Shaperon-g/AutoWatering-ch32v003/src/core/ch32v00x.h

/********************************** (C) COPYRIGHT  *******************************
 * File Name          : ch32v00x.h
 * Author             : Shaperon
 * Version            : V1.0
 * Date               : 13/06/2026
 * Description        : CH32V00x Modified file
 *********************************************************************************
 * The original file was most likely copied from another chip somewhere 
 * does not match the datasheet, so I redid it.
 * P.S. I also cleaned up a bit of the junk, so this
 * **NOT INTERCHANGEABLE with the official SDK and SPL**
 * 
 * Оригинальный файл скорее всего скопипащен с другого чипа и где-то 
 * несоответствует даташиту, поэтому я его переделал.
 * p.s. Я в целом еще немного мусора почистил, так что это 
 * **НЕ ВЗАИМОЗАМЕНЯЕМО с оф. SDK и SPL** 
 *******************************************************************************/
#ifndef __CH32V00x_H
#define __CH32V00x_H

#ifdef __cplusplus
extern "C" {
#endif

/* Interrupt Number Definition, according to the selected device */
typedef enum IRQn
{
    /******  RISC-V Processor Exceptions Numbers *******************************************************/
    NonMaskableInt_IRQn = 2, /* 2 Non Maskable Interrupt                             */
    EXC_IRQn = 3,            /* 3 Exception Interrupt                                */
    SysTick_IRQn = 12,       /* 12 System timer Interrupt                            */
    Software_IRQn = 14,      /* 14 software Interrupt                                */

    /******  RISC-V specific Interrupt Numbers *********************************************************/
    WWDG_IRQn = 16,          /* Window WatchDog Interrupt                            */
    PVD_IRQn = 17,           /* PVD through EXTI Line detection Interrupt            */
    FLASH_IRQn = 18,         /* FLASH global Interrupt                               */
    RCC_IRQn = 19,           /* RCC global Interrupt                                 */
    EXTI7_0_IRQn = 20,       /* External Line[7:0] Interrupts                        */
    AWU_IRQn = 21,           /* AWU global Interrupt                                 */
    DMA1_Channel1_IRQn = 22, /* DMA1 Channel 1 global Interrupt                      */
    DMA1_Channel2_IRQn = 23, /* DMA1 Channel 2 global Interrupt                      */
    DMA1_Channel3_IRQn = 24, /* DMA1 Channel 3 global Interrupt                      */
    DMA1_Channel4_IRQn = 25, /* DMA1 Channel 4 global Interrupt                      */
    DMA1_Channel5_IRQn = 26, /* DMA1 Channel 5 global Interrupt                      */
    DMA1_Channel6_IRQn = 27, /* DMA1 Channel 6 global Interrupt                      */
    DMA1_Channel7_IRQn = 28, /* DMA1 Channel 7 global Interrupt                      */
    ADC_IRQn = 29,           /* ADC global Interrupt                                 */
    I2C1_EV_IRQn = 30,       /* I2C1 Event Interrupt                                 */
    I2C1_ER_IRQn = 31,       /* I2C1 Error Interrupt                                 */
    USART1_IRQn = 32,        /* USART1 global Interrupt                              */
    SPI1_IRQn = 33,          /* SPI1 global Interrupt                                */
    TIM1_BRK_IRQn = 34,      /* TIM1 Break Interrupt                                 */
    TIM1_UP_IRQn = 35,       /* TIM1 Update Interrupt                                */
    TIM1_TRG_COM_IRQn = 36,  /* TIM1 Trigger and Commutation Interrupt               */
    TIM1_CC_IRQn = 37,       /* TIM1 Capture Compare Interrupt                       */
    TIM2_IRQn = 38,          /* TIM2 global Interrupt                                */

} IRQn_Type;

#define HardFault_IRQn    EXC_IRQn

#include <stdint.h>
#include <core_riscv.h>
//#include <system_ch32v00x.h>

/* Analog to Digital Converter */
typedef struct
{
    __IO uint32_t STATR;
    __IO uint32_t CTLR1;
    __IO uint32_t CTLR2;
    __IO uint32_t SAMPTR1;
    __IO uint32_t SAMPTR2;
    __IO uint32_t IOFR1;
    __IO uint32_t IOFR2;
    __IO uint32_t IOFR3;
    __IO uint32_t IOFR4;
    __IO uint32_t WDHTR;
    __IO uint32_t WDLTR;
    __IO uint32_t RSQR1;
    __IO uint32_t RSQR2;
    __IO uint32_t RSQR3;
    __IO uint32_t ISQR;
    __IO uint32_t IDATAR1;
    __IO uint32_t IDATAR2;
    __IO uint32_t IDATAR3;
    __IO uint32_t IDATAR4;
    __IO uint32_t RDATAR;
    __IO uint32_t DLYR;
} ADC_TypeDef;

/* Debug MCU */
typedef struct
{
    __IO uint32_t CFGR0;
    __IO uint32_t CFGR1;
} DBGMCU_TypeDef;

/* DMA Controller */
typedef struct
{
    __IO uint32_t CFGR;
    __IO uint32_t CNTR;
    __IO uint32_t PADDR;
    __IO uint32_t MADDR;
} DMA_Channel_TypeDef;

typedef struct
{
    __IO uint32_t INTFR;
    __IO uint32_t INTFCR;
} DMA_TypeDef;

/* External Interrupt/Event Controller */
typedef struct
{
    __IO uint32_t INTENR;
    __IO uint32_t EVENR;
    __IO uint32_t RTENR;
    __IO uint32_t FTENR;
    __IO uint32_t SWIEVR;
    __IO uint32_t INTFR;
} EXTI_TypeDef;

/* FLASH Registers */
typedef struct
{
    __IO uint32_t ACTLR;
    __IO uint32_t KEYR;
    __IO uint32_t OBKEYR;
    __IO uint32_t STATR;
    __IO uint32_t CTLR;
    __IO uint32_t ADDR;
    __IO uint32_t RESERVED;
    __IO uint32_t OBR;
    __IO uint32_t WPR;
    __IO uint32_t MODEKEYR;
    __IO uint32_t BOOT_MODEKEYR;
} FLASH_TypeDef;

/* Option Bytes Registers */
typedef struct
{
    __IO uint16_t RDPR;
    __IO uint16_t USER;
    __IO uint16_t DATA0;
    __IO uint16_t DATA1;
    __IO uint16_t WRPR0;
    __IO uint16_t WRPR1;
} OB_TypeDef;

/* General Purpose I/O */
typedef struct
{
    __IO uint32_t CFGLR;
    __IO uint32_t CFGHR;
    __IO uint32_t INDR;
    __IO uint32_t OUTDR;
    __IO uint32_t BSHR;
    __IO uint32_t BCR;
    __IO uint32_t LCKR;
} GPIO_TypeDef;

/* Alternate Function I/O */
typedef struct
{
    uint32_t RESERVED0;
    __IO uint32_t PCFR1;
    __IO uint32_t EXTICR;
} AFIO_TypeDef;

/* Inter Integrated Circuit Interface */
typedef struct
{
    __IO uint16_t CTLR1;
    uint16_t      RESERVED0;
    __IO uint16_t CTLR2;
    uint16_t      RESERVED1;
    __IO uint16_t OADDR1;
    uint16_t      RESERVED2;
    __IO uint16_t OADDR2;
    uint16_t      RESERVED3;
    __IO uint16_t DATAR;
    uint16_t      RESERVED4;
    __IO uint16_t STAR1;
    uint16_t      RESERVED5;
    __IO uint16_t STAR2;
    uint16_t      RESERVED6;
    __IO uint16_t CKCFGR;
    uint16_t      RESERVED7;
} I2C_TypeDef;

/* Independent WatchDog */
typedef struct
{
    __IO uint32_t CTLR;
    __IO uint32_t PSCR;
    __IO uint32_t RLDR;
    __IO uint32_t STATR;
} IWDG_TypeDef;

/* Power Control */
typedef struct
{
    __IO uint32_t CTLR;
    __IO uint32_t CSR;
    __IO uint32_t AWUCSR;
    __IO uint32_t AWUWR;
    __IO uint32_t AWUPSC;
} PWR_TypeDef;

/* Reset and Clock Control */
typedef struct
{
    __IO uint32_t CTLR;
    __IO uint32_t CFGR0;
    __IO uint32_t INTR;
    __IO uint32_t APB2PRSTR;
    __IO uint32_t APB1PRSTR;
    __IO uint32_t AHBPCENR;
    __IO uint32_t APB2PCENR;
    __IO uint32_t APB1PCENR;
    __IO uint32_t RESERVED0;
    __IO uint32_t RSTSCKR;
} RCC_TypeDef;

/* Serial Peripheral Interface */
typedef struct
{
    __IO uint16_t CTLR1;
    uint16_t      RESERVED0;
    __IO uint16_t CTLR2;
    uint16_t      RESERVED1;
    __IO uint16_t STATR;
    uint16_t      RESERVED2;
    __IO uint16_t DATAR;
    uint16_t      RESERVED3;
    __IO uint16_t CRCR;
    uint16_t      RESERVED4;
    __IO uint16_t RCRCR;
    uint16_t      RESERVED5;
    __IO uint16_t TCRCR;
    uint16_t      RESERVED6;
    uint32_t      RESERVED7;
    uint32_t      RESERVED8;
    __IO uint16_t HSCR;
    uint16_t      RESERVED9;
} SPI_TypeDef;

/* TIM */
typedef struct
{
    __IO uint16_t CTLR1;
    uint16_t      RESERVED0;
    __IO uint16_t CTLR2;
    uint16_t      RESERVED1;
    __IO uint16_t SMCFGR;
    uint16_t      RESERVED2;
    __IO uint16_t DMAINTENR;
    uint16_t      RESERVED3;
    __IO uint16_t INTFR;
    uint16_t      RESERVED4;
    __IO uint16_t SWEVGR;
    uint16_t      RESERVED5;
    __IO uint16_t CHCTLR1;
    uint16_t      RESERVED6;
    __IO uint16_t CHCTLR2;
    uint16_t      RESERVED7;
    __IO uint16_t CCER;
    uint16_t      RESERVED8;
    __IO uint16_t CNT;
    uint16_t      RESERVED9;
    __IO uint16_t PSC;
    uint16_t      RESERVED10;
    __IO uint16_t ATRLR;
    uint16_t      RESERVED11;
    __IO uint16_t RPTCR;
    uint16_t      RESERVED12;
    __IO uint32_t CH1CVR;
    __IO uint32_t CH2CVR;
    __IO uint32_t CH3CVR;
    __IO uint32_t CH4CVR;
    __IO uint16_t BDTR;
    uint16_t      RESERVED13;
    __IO uint16_t DMACFGR;
    uint16_t      RESERVED14;
    __IO uint16_t DMAADR;
    uint16_t      RESERVED15;
} TIM_TypeDef;

/* Universal Synchronous Asynchronous Receiver Transmitter */
typedef struct
{
    __IO uint16_t STATR;
    uint16_t      RESERVED0;
    __IO uint16_t DATAR;
    uint16_t      RESERVED1;
    __IO uint16_t BRR;
    uint16_t      RESERVED2;
    __IO uint16_t CTLR1;
    uint16_t      RESERVED3;
    __IO uint16_t CTLR2;
    uint16_t      RESERVED4;
    __IO uint16_t CTLR3;
    uint16_t      RESERVED5;
    __IO uint16_t GPR;
    uint16_t      RESERVED6;
} USART_TypeDef;

/* Window WatchDog */
typedef struct
{
    __IO uint32_t CTLR;
    __IO uint32_t CFGR;
    __IO uint32_t STATR;
} WWDG_TypeDef;

/* Enhanced Registers */
typedef struct
{
    __IO uint32_t EXTEN_CTR;
} EXTEN_TypeDef;

/* Peripheral memory map */
#define FLASH_BASE                              ((uint32_t)0x08000000) /* FLASH base address in the alias region */
#define SRAM_BASE                               ((uint32_t)0x20000000) /* SRAM base address in the alias region */
#define PERIPH_BASE                             ((uint32_t)0x40000000) /* Peripheral base address in the alias region */

#define APB1PERIPH_BASE                         (PERIPH_BASE)
#define APB2PERIPH_BASE                         (PERIPH_BASE + 0x10000)
#define AHBPERIPH_BASE                          (PERIPH_BASE + 0x20000)

#define TIM2_BASE                               (APB1PERIPH_BASE + 0x0000)
#define WWDG_BASE                               (APB1PERIPH_BASE + 0x2C00)
#define IWDG_BASE                               (APB1PERIPH_BASE + 0x3000)
#define I2C1_BASE                               (APB1PERIPH_BASE + 0x5400)
#define PWR_BASE                                (APB1PERIPH_BASE + 0x7000)

#define AFIO_BASE                               (APB2PERIPH_BASE + 0x0000)
#define EXTI_BASE                               (APB2PERIPH_BASE + 0x0400)
#define GPIOA_BASE                              (APB2PERIPH_BASE + 0x0800)
#define GPIOC_BASE                              (APB2PERIPH_BASE + 0x1000)
#define GPIOD_BASE                              (APB2PERIPH_BASE + 0x1400)
#define ADC1_BASE                               (APB2PERIPH_BASE + 0x2400)
#define TIM1_BASE                               (APB2PERIPH_BASE + 0x2C00)
#define SPI1_BASE                               (APB2PERIPH_BASE + 0x3000)
#define USART1_BASE                             (APB2PERIPH_BASE + 0x3800)

#define DMA1_BASE                               (AHBPERIPH_BASE + 0x0000)
#define DMA1_Channel1_BASE                      (AHBPERIPH_BASE + 0x0008)
#define DMA1_Channel2_BASE                      (AHBPERIPH_BASE + 0x001C)
#define DMA1_Channel3_BASE                      (AHBPERIPH_BASE + 0x0030)
#define DMA1_Channel4_BASE                      (AHBPERIPH_BASE + 0x0044)
#define DMA1_Channel5_BASE                      (AHBPERIPH_BASE + 0x0058)
#define DMA1_Channel6_BASE                      (AHBPERIPH_BASE + 0x006C)
#define DMA1_Channel7_BASE                      (AHBPERIPH_BASE + 0x0080)
#define RCC_BASE                                (AHBPERIPH_BASE + 0x1000)

#define FLASH_R_BASE                            (AHBPERIPH_BASE + 0x2000) /* Flash registers base address */
#define OB_BASE                                 ((uint32_t)0x1FFFF800)    /* Flash Option Bytes base address */
#define EXTEN_BASE                              ((uint32_t)0x40023800)

/* Peripheral declaration */
#define TIM2                                    ((TIM_TypeDef *)TIM2_BASE)
#define WWDG                                    ((WWDG_TypeDef *)WWDG_BASE)
#define IWDG                                    ((IWDG_TypeDef *)IWDG_BASE)
#define I2C1                                    ((I2C_TypeDef *)I2C1_BASE)
#define PWR                                     ((PWR_TypeDef *)PWR_BASE)
#define AFIO                                    ((AFIO_TypeDef *)AFIO_BASE)
#define EXTI                                    ((EXTI_TypeDef *)EXTI_BASE)
#define GPIOA                                   ((GPIO_TypeDef *)GPIOA_BASE)
#define GPIOC                                   ((GPIO_TypeDef *)GPIOC_BASE)
#define GPIOD                                   ((GPIO_TypeDef *)GPIOD_BASE)
#define ADC1                                    ((ADC_TypeDef *)ADC1_BASE)
#define TIM1                                    ((TIM_TypeDef *)TIM1_BASE)
#define SPI1                                    ((SPI_TypeDef *)SPI1_BASE)
#define USART1                                  ((USART_TypeDef *)USART1_BASE)
#define DMA1                                    ((DMA_TypeDef *)DMA1_BASE)
#define DMA1_Channel1                           ((DMA_Channel_TypeDef *)DMA1_Channel1_BASE)
#define DMA1_Channel2                           ((DMA_Channel_TypeDef *)DMA1_Channel2_BASE)
#define DMA1_Channel3                           ((DMA_Channel_TypeDef *)DMA1_Channel3_BASE)
#define DMA1_Channel4                           ((DMA_Channel_TypeDef *)DMA1_Channel4_BASE)
#define DMA1_Channel5                           ((DMA_Channel_TypeDef *)DMA1_Channel5_BASE)
#define DMA1_Channel6                           ((DMA_Channel_TypeDef *)DMA1_Channel6_BASE)
#define DMA1_Channel7                           ((DMA_Channel_TypeDef *)DMA1_Channel7_BASE)
#define RCC                                     ((RCC_TypeDef *)RCC_BASE)
#define FLASH                                   ((FLASH_TypeDef *)FLASH_R_BASE)
#define OB                                      ((OB_TypeDef *)OB_BASE)
#define EXTEN                                   ((EXTEN_TypeDef *)EXTEN_BASE)

/******************************************************************************/
/*                         Peripheral Registers Bits Definition               */
/******************************************************************************/

/******************************************************************************/
/*                        Analog to Digital Converter                         */
/******************************************************************************/

/********************  Bit definition for ADC_STATR register  ********************/
#define ADC_AWD                                 ((uint8_t)0x01) /* Analog watchdog flag */
#define ADC_EOC                                 ((uint8_t)0x02) /* End of conversion */
#define ADC_JEOC                                ((uint8_t)0x04) /* Injected channel end of conversion */
#define ADC_JSTRT                               ((uint8_t)0x08) /* Injected channel Start flag */
#define ADC_STRT                                ((uint8_t)0x10) /* Regular channel Start flag */

/*******************  Bit definition for ADC_CTLR1 register  ********************/
#define ADC_AWDCH                               ((uint32_t)0x0000001F) /* AWDCH[4:0] bits (Analog watchdog channel select bits) */
#define ADC_AWDCH_0                             ((uint32_t)0x00000001) /* Bit 0 */
#define ADC_AWDCH_1                             ((uint32_t)0x00000002) /* Bit 1 */
#define ADC_AWDCH_2                             ((uint32_t)0x00000004) /* Bit 2 */
#define ADC_AWDCH_3                             ((uint32_t)0x00000008) /* Bit 3 */
#define ADC_AWDCH_4                             ((uint32_t)0x00000010) /* Bit 4 */

#define ADC_EOCIE                               ((uint32_t)0x00000020) /* Interrupt enable for EOC */
#define ADC_AWDIE                               ((uint32_t)0x00000040) /* Analog Watchdog interrupt enable */
#define ADC_JEOCIE                              ((uint32_t)0x00000080) /* Interrupt enable for injected channels */
#define ADC_SCAN                                ((uint32_t)0x00000100) /* Scan mode */
#define ADC_AWDSGL                              ((uint32_t)0x00000200) /* Enable the watchdog on a single channel in scan mode */
#define ADC_JAUTO                               ((uint32_t)0x00000400) /* Automatic injected group conversion */
#define ADC_DISCEN                              ((uint32_t)0x00000800) /* Discontinuous mode on regular channels */
#define ADC_JDISCEN                             ((uint32_t)0x00001000) /* Discontinuous mode on injected channels */

#define ADC_DISCNUM                             ((uint32_t)0x0000E000) /* DISCNUM[2:0] bits (Discontinuous mode channel count) */
#define ADC_DISCNUM_0                           ((uint32_t)0x00002000) /* Bit 0 */
#define ADC_DISCNUM_1                           ((uint32_t)0x00004000) /* Bit 1 */
#define ADC_DISCNUM_2                           ((uint32_t)0x00008000) /* Bit 2 */

#define ADC_JAWDEN                              ((uint32_t)0x00400000) /* Analog watchdog enable on injected channels */
#define ADC_AWDEN                               ((uint32_t)0x00800000) /* Analog watchdog enable on regular channels */

#define ADC_CALVOL                              ((uint32_t)0x06000000) /* Calibration voltage selection */
#define ADC_CALVOL_0                            ((uint32_t)0x02000000) /* Bit 0 */
#define ADC_CALVOL_1                            ((uint32_t)0x04000000) /* Bit 1 */

/*******************  Bit definition for ADC_CTLR2 register  ********************/
#define ADC_ADON                                ((uint32_t)0x00000001) /* A/D Converter ON / OFF */
#define ADC_CONT                                ((uint32_t)0x00000002) /* Continuous Conversion */
#define ADC_CAL                                 ((uint32_t)0x00000004) /* A/D Calibration */
#define ADC_RSTCAL                              ((uint32_t)0x00000008) /* Reset Calibration */
#define ADC_DMA                                 ((uint32_t)0x00000100) /* Direct Memory access mode */
#define ADC_ALIGN                               ((uint32_t)0x00000800) /* Data Alignment */

#define ADC_JEXTSEL                             ((uint32_t)0x00007000) /* JEXTSEL[2:0] bits (External event select for injected group) */
#define ADC_JEXTSEL_0                           ((uint32_t)0x00001000) /* Bit 0 */
#define ADC_JEXTSEL_1                           ((uint32_t)0x00002000) /* Bit 1 */
#define ADC_JEXTSEL_2                           ((uint32_t)0x00004000) /* Bit 2 */

#define ADC_JEXTTRIG                            ((uint32_t)0x00008000) /* External Trigger Conversion mode for injected channels */

#define ADC_EXTSEL                              ((uint32_t)0x000E0000) /* EXTSEL[2:0] bits (External Event Select for regular group) */
#define ADC_EXTSEL_0                            ((uint32_t)0x00020000) /* Bit 0 */
#define ADC_EXTSEL_1                            ((uint32_t)0x00040000) /* Bit 1 */
#define ADC_EXTSEL_2                            ((uint32_t)0x00080000) /* Bit 2 */

#define ADC_EXTTRIG                             ((uint32_t)0x00100000) /* External Trigger Conversion mode for regular channels */
#define ADC_JSWSTART                            ((uint32_t)0x00200000) /* Start Conversion of injected channels */
#define ADC_SWSTART                             ((uint32_t)0x00400000) /* Start Conversion of regular channels */

/******************  Bit definition for ADC_SAMPTR1 register  *******************/
#define ADC_SMP10                               ((uint32_t)0x00000007) /* SMP10[2:0] bits (Channel 10 Sample time selection) */
#define ADC_SMP10_0                             ((uint32_t)0x00000001) /* Bit 0 */
#define ADC_SMP10_1                             ((uint32_t)0x00000002) /* Bit 1 */
#define ADC_SMP10_2                             ((uint32_t)0x00000004) /* Bit 2 */

#define ADC_SMP11                               ((uint32_t)0x00000038) /* SMP11[2:0] bits (Channel 11 Sample time selection) */
#define ADC_SMP11_0                             ((uint32_t)0x00000008) /* Bit 0 */
#define ADC_SMP11_1                             ((uint32_t)0x00000010) /* Bit 1 */
#define ADC_SMP11_2                             ((uint32_t)0x00000020) /* Bit 2 */

#define ADC_SMP12                               ((uint32_t)0x000001C0) /* SMP12[2:0] bits (Channel 12 Sample time selection) */
#define ADC_SMP12_0                             ((uint32_t)0x00000040) /* Bit 0 */
#define ADC_SMP12_1                             ((uint32_t)0x00000080) /* Bit 1 */
#define ADC_SMP12_2                             ((uint32_t)0x00000100) /* Bit 2 */

#define ADC_SMP13                               ((uint32_t)0x00000E00) /* SMP13[2:0] bits (Channel 13 Sample time selection) */
#define ADC_SMP13_0                             ((uint32_t)0x00000200) /* Bit 0 */
#define ADC_SMP13_1                             ((uint32_t)0x00000400) /* Bit 1 */
#define ADC_SMP13_2                             ((uint32_t)0x00000800) /* Bit 2 */

#define ADC_SMP14                               ((uint32_t)0x00007000) /* SMP14[2:0] bits (Channel 14 Sample time selection) */
#define ADC_SMP14_0                             ((uint32_t)0x00001000) /* Bit 0 */
#define ADC_SMP14_1                             ((uint32_t)0x00002000) /* Bit 1 */
#define ADC_SMP14_2                             ((uint32_t)0x00004000) /* Bit 2 */

#define ADC_SMP15                               ((uint32_t)0x00038000) /* SMP15[2:0] bits (Channel 15 Sample time selection) */
#define ADC_SMP15_0                             ((uint32_t)0x00008000) /* Bit 0 */
#define ADC_SMP15_1                             ((uint32_t)0x00010000) /* Bit 1 */
#define ADC_SMP15_2                             ((uint32_t)0x00020000) /* Bit 2 */

#define ADC_SMP16                               ((uint32_t)0x001C0000) /* SMP16[2:0] bits (Channel 16 Sample time selection) */
#define ADC_SMP16_0                             ((uint32_t)0x00040000) /* Bit 0 */
#define ADC_SMP16_1                             ((uint32_t)0x00080000) /* Bit 1 */
#define ADC_SMP16_2                             ((uint32_t)0x00100000) /* Bit 2 */

#define ADC_SMP17                               ((uint32_t)0x00E00000) /* SMP17[2:0] bits (Channel 17 Sample time selection) */
#define ADC_SMP17_0                             ((uint32_t)0x00200000) /* Bit 0 */
#define ADC_SMP17_1                             ((uint32_t)0x00400000) /* Bit 1 */
#define ADC_SMP17_2                             ((uint32_t)0x00800000) /* Bit 2 */

/******************  Bit definition for ADC_SAMPTR2 register  *******************/
#define ADC_SMP0                                ((uint32_t)0x00000007) /* SMP0[2:0] bits (Channel 0 Sample time selection) */
#define ADC_SMP0_0                              ((uint32_t)0x00000001) /* Bit 0 */
#define ADC_SMP0_1                              ((uint32_t)0x00000002) /* Bit 1 */
#define ADC_SMP0_2                              ((uint32_t)0x00000004) /* Bit 2 */

#define ADC_SMP1                                ((uint32_t)0x00000038) /* SMP1[2:0] bits (Channel 1 Sample time selection) */
#define ADC_SMP1_0                              ((uint32_t)0x00000008) /* Bit 0 */
#define ADC_SMP1_1                              ((uint32_t)0x00000010) /* Bit 1 */
#define ADC_SMP1_2                              ((uint32_t)0x00000020) /* Bit 2 */

#define ADC_SMP2                                ((uint32_t)0x000001C0) /* SMP2[2:0] bits (Channel 2 Sample time selection) */
#define ADC_SMP2_0                              ((uint32_t)0x00000040) /* Bit 0 */
#define ADC_SMP2_1                              ((uint32_t)0x00000080) /* Bit 1 */
#define ADC_SMP2_2                              ((uint32_t)0x00000100) /* Bit 2 */

#define ADC_SMP3                                ((uint32_t)0x00000E00) /* SMP3[2:0] bits (Channel 3 Sample time selection) */
#define ADC_SMP3_0                              ((uint32_t)0x00000200) /* Bit 0 */
#define ADC_SMP3_1                              ((uint32_t)0x00000400) /* Bit 1 */
#define ADC_SMP3_2                              ((uint32_t)0x00000800) /* Bit 2 */

#define ADC_SMP4                                ((uint32_t)0x00007000) /* SMP4[2:0] bits (Channel 4 Sample time selection) */
#define ADC_SMP4_0                              ((uint32_t)0x00001000) /* Bit 0 */
#define ADC_SMP4_1                              ((uint32_t)0x00002000) /* Bit 1 */
#define ADC_SMP4_2                              ((uint32_t)0x00004000) /* Bit 2 */

#define ADC_SMP5                                ((uint32_t)0x00038000) /* SMP5[2:0] bits (Channel 5 Sample time selection) */
#define ADC_SMP5_0                              ((uint32_t)0x00008000) /* Bit 0 */
#define ADC_SMP5_1                              ((uint32_t)0x00010000) /* Bit 1 */
#define ADC_SMP5_2                              ((uint32_t)0x00020000) /* Bit 2 */

#define ADC_SMP6                                ((uint32_t)0x001C0000) /* SMP6[2:0] bits (Channel 6 Sample time selection) */
#define ADC_SMP6_0                              ((uint32_t)0x00040000) /* Bit 0 */
#define ADC_SMP6_1                              ((uint32_t)0x00080000) /* Bit 1 */
#define ADC_SMP6_2                              ((uint32_t)0x00100000) /* Bit 2 */

#define ADC_SMP7                                ((uint32_t)0x00E00000) /* SMP7[2:0] bits (Channel 7 Sample time selection) */
#define ADC_SMP7_0                              ((uint32_t)0x00200000) /* Bit 0 */
#define ADC_SMP7_1                              ((uint32_t)0x00400000) /* Bit 1 */
#define ADC_SMP7_2                              ((uint32_t)0x00800000) /* Bit 2 */

#define ADC_SMP8                                ((uint32_t)0x07000000) /* SMP8[2:0] bits (Channel 8 Sample time selection) */
#define ADC_SMP8_0                              ((uint32_t)0x01000000) /* Bit 0 */
#define ADC_SMP8_1                              ((uint32_t)0x02000000) /* Bit 1 */
#define ADC_SMP8_2                              ((uint32_t)0x04000000) /* Bit 2 */

#define ADC_SMP9                                ((uint32_t)0x38000000) /* SMP9[2:0] bits (Channel 9 Sample time selection) */
#define ADC_SMP9_0                              ((uint32_t)0x08000000) /* Bit 0 */
#define ADC_SMP9_1                              ((uint32_t)0x10000000) /* Bit 1 */
#define ADC_SMP9_2                              ((uint32_t)0x20000000) /* Bit 2 */

/******************  Bit definition for ADC_IOFR1 register  *******************/
#define ADC_JOFFSET1                            ((uint16_t)0x0FFF) /* Data offset for injected channel 1 */

/******************  Bit definition for ADC_IOFR2 register  *******************/
#define ADC_JOFFSET2                            ((uint16_t)0x0FFF) /* Data offset for injected channel 2 */

/******************  Bit definition for ADC_IOFR3 register  *******************/
#define ADC_JOFFSET3                            ((uint16_t)0x0FFF) /* Data offset for injected channel 3 */

/******************  Bit definition for ADC_IOFR4 register  *******************/
#define ADC_JOFFSET4                            ((uint16_t)0x0FFF) /* Data offset for injected channel 4 */

/*******************  Bit definition for ADC_WDHTR register  ********************/
#define ADC_HT                                  ((uint16_t)0x0FFF) /* Analog watchdog high threshold */

/*******************  Bit definition for ADC_WDLTR register  ********************/
#define ADC_LT                                  ((uint16_t)0x0FFF) /* Analog watchdog low threshold */

/*******************  Bit definition for ADC_RSQR1 register  *******************/
#define ADC_SQ13                                ((uint32_t)0x0000001F) /* SQ13[4:0] bits (13th conversion in regular sequence) */
#define ADC_SQ13_0                              ((uint32_t)0x00000001) /* Bit 0 */
#define ADC_SQ13_1                              ((uint32_t)0x00000002) /* Bit 1 */
#define ADC_SQ13_2                              ((uint32_t)0x00000004) /* Bit 2 */
#define ADC_SQ13_3                              ((uint32_t)0x00000008) /* Bit 3 */
#define ADC_SQ13_4                              ((uint32_t)0x00000010) /* Bit 4 */

#define ADC_SQ14                                ((uint32_t)0x000003E0) /* SQ14[4:0] bits (14th conversion in regular sequence) */
#define ADC_SQ14_0                              ((uint32_t)0x00000020) /* Bit 0 */
#define ADC_SQ14_1                              ((uint32_t)0x00000040) /* Bit 1 */
#define ADC_SQ14_2                              ((uint32_t)0x00000080) /* Bit 2 */
#define ADC_SQ14_3                              ((uint32_t)0x00000100) /* Bit 3 */
#define ADC_SQ14_4                              ((uint32_t)0x00000200) /* Bit 4 */

#define ADC_SQ15                                ((uint32_t)0x00007C00) /* SQ15[4:0] bits (15th conversion in regular sequence) */
#define ADC_SQ15_0                              ((uint32_t)0x00000400) /* Bit 0 */
#define ADC_SQ15_1                              ((uint32_t)0x00000800) /* Bit 1 */
#define ADC_SQ15_2                              ((uint32_t)0x00001000) /* Bit 2 */
#define ADC_SQ15_3                              ((uint32_t)0x00002000) /* Bit 3 */
#define ADC_SQ15_4                              ((uint32_t)0x00004000) /* Bit 4 */

#define ADC_SQ16                                ((uint32_t)0x000F8000) /* SQ16[4:0] bits (16th conversion in regular sequence) */
#define ADC_SQ16_0                              ((uint32_t)0x00008000) /* Bit 0 */
#define ADC_SQ16_1                              ((uint32_t)0x00010000) /* Bit 1 */
#define ADC_SQ16_2                              ((uint32_t)0x00020000) /* Bit 2 */
#define ADC_SQ16_3                              ((uint32_t)0x00040000) /* Bit 3 */
#define ADC_SQ16_4                              ((uint32_t)0x00080000) /* Bit 4 */

#define ADC_L                                   ((uint32_t)0x00F00000) /* L[3:0] bits (Regular channel sequence length) */
#define ADC_L_0                                 ((uint32_t)0x00100000) /* Bit 0 */
#define ADC_L_1                                 ((uint32_t)0x00200000) /* Bit 1 */
#define ADC_L_2                                 ((uint32_t)0x00400000) /* Bit 2 */
#define ADC_L_3                                 ((uint32_t)0x00800000) /* Bit 3 */

/*******************  Bit definition for ADC_RSQR2 register  *******************/
#define ADC_SQ7                                 ((uint32_t)0x0000001F) /* SQ7[4:0] bits (7th conversion in regular sequence) */
#define ADC_SQ7_0                               ((uint32_t)0x00000001) /* Bit 0 */
#define ADC_SQ7_1                               ((uint32_t)0x00000002) /* Bit 1 */
#define ADC_SQ7_2                               ((uint32_t)0x00000004) /* Bit 2 */
#define ADC_SQ7_3                               ((uint32_t)0x00000008) /* Bit 3 */
#define ADC_SQ7_4                               ((uint32_t)0x00000010) /* Bit 4 */

#define ADC_SQ8                                 ((uint32_t)0x000003E0) /* SQ8[4:0] bits (8th conversion in regular sequence) */
#define ADC_SQ8_0                               ((uint32_t)0x00000020) /* Bit 0 */
#define ADC_SQ8_1                               ((uint32_t)0x00000040) /* Bit 1 */
#define ADC_SQ8_2                               ((uint32_t)0x00000080) /* Bit 2 */
#define ADC_SQ8_3                               ((uint32_t)0x00000100) /* Bit 3 */
#define ADC_SQ8_4                               ((uint32_t)0x00000200) /* Bit 4 */

#define ADC_SQ9                                 ((uint32_t)0x00007C00) /* SQ9[4:0] bits (9th conversion in regular sequence) */
#define ADC_SQ9_0                               ((uint32_t)0x00000400) /* Bit 0 */
#define ADC_SQ9_1                               ((uint32_t)0x00000800) /* Bit 1 */
#define ADC_SQ9_2                               ((uint32_t)0x00001000) /* Bit 2 */
#define ADC_SQ9_3                               ((uint32_t)0x00002000) /* Bit 3 */
#define ADC_SQ9_4                               ((uint32_t)0x00004000) /* Bit 4 */

#define ADC_SQ10                                ((uint32_t)0x000F8000) /* SQ10[4:0] bits (10th conversion in regular sequence) */
#define ADC_SQ10_0                              ((uint32_t)0x00008000) /* Bit 0 */
#define ADC_SQ10_1                              ((uint32_t)0x00010000) /* Bit 1 */
#define ADC_SQ10_2                              ((uint32_t)0x00020000) /* Bit 2 */
#define ADC_SQ10_3                              ((uint32_t)0x00040000) /* Bit 3 */
#define ADC_SQ10_4                              ((uint32_t)0x00080000) /* Bit 4 */

#define ADC_SQ11                                ((uint32_t)0x01F00000) /* SQ11[4:0] bits (11th conversion in regular sequence) */
#define ADC_SQ11_0                              ((uint32_t)0x00100000) /* Bit 0 */
#define ADC_SQ11_1                              ((uint32_t)0x00200000) /* Bit 1 */
#define ADC_SQ11_2                              ((uint32_t)0x00400000) /* Bit 2 */
#define ADC_SQ11_3                              ((uint32_t)0x00800000) /* Bit 3 */
#define ADC_SQ11_4                              ((uint32_t)0x01000000) /* Bit 4 */

#define ADC_SQ12                                ((uint32_t)0x3E000000) /* SQ12[4:0] bits (12th conversion in regular sequence) */
#define ADC_SQ12_0                              ((uint32_t)0x02000000) /* Bit 0 */
#define ADC_SQ12_1                              ((uint32_t)0x04000000) /* Bit 1 */
#define ADC_SQ12_2                              ((uint32_t)0x08000000) /* Bit 2 */
#define ADC_SQ12_3                              ((uint32_t)0x10000000) /* Bit 3 */
#define ADC_SQ12_4                              ((uint32_t)0x20000000) /* Bit 4 */

/*******************  Bit definition for ADC_RSQR3 register  *******************/
#define ADC_SQ1                                 ((uint32_t)0x0000001F) /* SQ1[4:0] bits (1st conversion in regular sequence) */
#define ADC_SQ1_0                               ((uint32_t)0x00000001) /* Bit 0 */
#define ADC_SQ1_1                               ((uint32_t)0x00000002) /* Bit 1 */
#define ADC_SQ1_2                               ((uint32_t)0x00000004) /* Bit 2 */
#define ADC_SQ1_3                               ((uint32_t)0x00000008) /* Bit 3 */
#define ADC_SQ1_4                               ((uint32_t)0x00000010) /* Bit 4 */

#define ADC_SQ2                                 ((uint32_t)0x000003E0) /* SQ2[4:0] bits (2nd conversion in regular sequence) */
#define ADC_SQ2_0                               ((uint32_t)0x00000020) /* Bit 0 */
#define ADC_SQ2_1                               ((uint32_t)0x00000040) /* Bit 1 */
#define ADC_SQ2_2                               ((uint32_t)0x00000080) /* Bit 2 */
#define ADC_SQ2_3                               ((uint32_t)0x00000100) /* Bit 3 */
#define ADC_SQ2_4                               ((uint32_t)0x00000200) /* Bit 4 */

#define ADC_SQ3                                 ((uint32_t)0x00007C00) /* SQ3[4:0] bits (3rd conversion in regular sequence) */
#define ADC_SQ3_0                               ((uint32_t)0x00000400) /* Bit 0 */
#define ADC_SQ3_1                               ((uint32_t)0x00000800) /* Bit 1 */
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
#define ADC_JSQ4_2                              ((uint32_t)0x00020000) /* Bit 2 */
#define ADC_JSQ4_3                              ((uint32_t)0x00040000) /* Bit 3 */
#define ADC_JSQ4_4                              ((uint32_t)0x00080000) /* Bit 4 */

#define ADC_JL                                  ((uint32_t)0x00300000) /* JL[1:0] bits (Injected Sequence length) */
#define ADC_JL_0                                ((uint32_t)0x00100000) /* Bit 0 */
#define ADC_JL_1                                ((uint32_t)0x00200000) /* Bit 1 */

/*******************  Bit definition for ADC_IDATAR1 register  *******************/
#define ADC_IDATAR1_JDATA                       ((uint16_t)0xFFFF) /* Injected data */

/*******************  Bit definition for ADC_IDATAR2 register  *******************/
#define ADC_IDATAR2_JDATA                       ((uint16_t)0xFFFF) /* Injected data */

/*******************  Bit definition for ADC_IDATAR3 register  *******************/
#define ADC_IDATAR3_JDATA                       ((uint16_t)0xFFFF) /* Injected data */

/*******************  Bit definition for ADC_IDATAR4 register  *******************/
#define ADC_IDATAR4_JDATA                       ((uint16_t)0xFFFF) /* Injected data */

/********************  Bit definition for ADC_RDATAR register  ********************/
#define ADC_RDATAR_DATA                         ((uint32_t)0x0000FFFF) /* Regular data */

/********************  Bit definition for ADC_DLYR register  ********************/
#define ADC_DLYR_DLYVLU                         ((uint32_t)0x0001FFFF) /* External trigger delay data */
#define ADC_DLYR_DLYSRC                         ((uint32_t)0x00020000) /* External trigger source delay selection */

/******************************************************************************/
/*                             DMA Controller                                 */
/******************************************************************************/

/*******************  Bit definition for DMA_INTFR register  ********************/
#define DMA_GIF1                                ((uint32_t)0x00000001) /* Channel 1 Global interrupt flag */
#define DMA_TCIF1                               ((uint32_t)0x00000002) /* Channel 1 Transfer Complete flag */
#define DMA_HTIF1                               ((uint32_t)0x00000004) /* Channel 1 Half Transfer flag */
#define DMA_TEIF1                               ((uint32_t)0x00000008) /* Channel 1 Transfer Error flag */
#define DMA_GIF2                                ((uint32_t)0x00000010) /* Channel 2 Global interrupt flag */
#define DMA_TCIF2                               ((uint32_t)0x00000020) /* Channel 2 Transfer Complete flag */
#define DMA_HTIF2                               ((uint32_t)0x00000040) /* Channel 2 Half Transfer flag */
#define DMA_TEIF2                               ((uint32_t)0x00000080) /* Channel 2 Transfer Error flag */
#define DMA_GIF3                                ((uint32_t)0x00000100) /* Channel 3 Global interrupt flag */
#define DMA_TCIF3                               ((uint32_t)0x00000200) /* Channel 3 Transfer Complete flag */
#define DMA_HTIF3                               ((uint32_t)0x00000400) /* Channel 3 Half Transfer flag */
#define DMA_TEIF3                               ((uint32_t)0x00000800) /* Channel 3 Transfer Error flag */
#define DMA_GIF4                                ((uint32_t)0x00001000) /* Channel 4 Global interrupt flag */
#define DMA_TCIF4                               ((uint32_t)0x00002000) /* Channel 4 Transfer Complete flag */
#define DMA_HTIF4                               ((uint32_t)0x00004000) /* Channel 4 Half Transfer flag */
#define DMA_TEIF4                               ((uint32_t)0x00008000) /* Channel 4 Transfer Error flag */
#define DMA_GIF5                                ((uint32_t)0x00010000) /* Channel 5 Global interrupt flag */
#define DMA_TCIF5                               ((uint32_t)0x00020000) /* Channel 5 Transfer Complete flag */
#define DMA_HTIF5                               ((uint32_t)0x00040000) /* Channel 5 Half Transfer flag */
#define DMA_TEIF5                               ((uint32_t)0x00080000) /* Channel 5 Transfer Error flag */
#define DMA_GIF6                                ((uint32_t)0x00100000) /* Channel 6 Global interrupt flag */
#define DMA_TCIF6                               ((uint32_t)0x00200000) /* Channel 6 Transfer Complete flag */
#define DMA_HTIF6                               ((uint32_t)0x00400000) /* Channel 6 Half Transfer flag */
#define DMA_TEIF6                               ((uint32_t)0x00800000) /* Channel 6 Transfer Error flag */
#define DMA_GIF7                                ((uint32_t)0x01000000) /* Channel 7 Global interrupt flag */
#define DMA_TCIF7                               ((uint32_t)0x02000000) /* Channel 7 Transfer Complete flag */
#define DMA_HTIF7                               ((uint32_t)0x04000000) /* Channel 7 Half Transfer flag */
#define DMA_TEIF7                               ((uint32_t)0x08000000) /* Channel 7 Transfer Error flag */

/*******************  Bit definition for DMA_INTFCR register  *******************/
#define DMA_CGIF1                               ((uint32_t)0x00000001) /* Channel 1 Global interrupt clear */
#define DMA_CTCIF1                              ((uint32_t)0x00000002) /* Channel 1 Transfer Complete clear */
#define DMA_CHTIF1                              ((uint32_t)0x00000004) /* Channel 1 Half Transfer clear */
#define DMA_CTEIF1                              ((uint32_t)0x00000008) /* Channel 1 Transfer Error clear */
#define DMA_CGIF2                               ((uint32_t)0x00000010) /* Channel 2 Global interrupt clear */
#define DMA_CTCIF2                              ((uint32_t)0x00000020) /* Channel 2 Transfer Complete clear */
#define DMA_CHTIF2                              ((uint32_t)0x00000040) /* Channel 2 Half Transfer clear */
#define DMA_CTEIF2                              ((uint32_t)0x00000080) /* Channel 2 Transfer Error clear */
#define DMA_CGIF3                               ((uint32_t)0x00000100) /* Channel 3 Global interrupt clear */
#define DMA_CTCIF3                              ((uint32_t)0x00000200) /* Channel 3 Transfer Complete clear */
#define DMA_CHTIF3                              ((uint32_t)0x00000400) /* Channel 3 Half Transfer clear */
#define DMA_CTEIF3                              ((uint32_t)0x00000800) /* Channel 3 Transfer Error clear */
#define DMA_CGIF4                               ((uint32_t)0x00001000) /* Channel 4 Global interrupt clear */
#define DMA_CTCIF4                              ((uint32_t)0x00002000) /* Channel 4 Transfer Complete clear */
#define DMA_CHTIF4                              ((uint32_t)0x00004000) /* Channel 4 Half Transfer clear */
#define DMA_CTEIF4                              ((uint32_t)0x00008000) /* Channel 4 Transfer Error clear */
#define DMA_CGIF5                               ((uint32_t)0x00010000) /* Channel 5 Global interrupt clear */
#define DMA_CTCIF5                              ((uint32_t)0x00020000) /* Channel 5 Transfer Complete clear */
#define DMA_CHTIF5                              ((uint32_t)0x00040000) /* Channel 5 Half Transfer clear */
#define DMA_CTEIF5                              ((uint32_t)0x00080000) /* Channel 5 Transfer Error clear */
#define DMA_CGIF6                               ((uint32_t)0x00100000) /* Channel 6 Global interrupt clear */
#define DMA_CTCIF6                              ((uint32_t)0x00200000) /* Channel 6 Transfer Complete clear */
#define DMA_CHTIF6                              ((uint32_t)0x00400000) /* Channel 6 Half Transfer clear */
#define DMA_CTEIF6                              ((uint32_t)0x00800000) /* Channel 6 Transfer Error clear */
#define DMA_CGIF7                               ((uint32_t)0x01000000) /* Channel 7 Global interrupt clear */
#define DMA_CTCIF7                              ((uint32_t)0x02000000) /* Channel 7 Transfer Complete clear */
#define DMA_CHTIF7                              ((uint32_t)0x04000000) /* Channel 7 Half Transfer clear */
#define DMA_CTEIF7                              ((uint32_t)0x08000000) /* Channel 7 Transfer Error clear */

/*******************  Bit definition for DMA_CFGR1 register  *******************/
#define DMA_CFGR1_EN                            ((uint16_t)0x0001) /* Channel enable*/
#define DMA_CFGR1_TCIE                          ((uint16_t)0x0002) /* Transfer complete interrupt enable */
#define DMA_CFGR1_HTIE                          ((uint16_t)0x0004) /* Half Transfer interrupt enable */
#define DMA_CFGR1_TEIE                          ((uint16_t)0x0008) /* Transfer error interrupt enable */
#define DMA_CFGR1_DIR                           ((uint16_t)0x0010) /* Data transfer direction */
#define DMA_CFGR1_CIRC                          ((uint16_t)0x0020) /* Circular mode */
#define DMA_CFGR1_PINC                          ((uint16_t)0x0040) /* Peripheral increment mode */
#define DMA_CFGR1_MINC                          ((uint16_t)0x0080) /* Memory increment mode */

#define DMA_CFGR1_PSIZE                         ((uint16_t)0x0300) /* PSIZE[1:0] bits (Peripheral size) */
#define DMA_CFGR1_PSIZE_0                       ((uint16_t)0x0100) /* Bit 0 */
#define DMA_CFGR1_PSIZE_1                       ((uint16_t)0x0200) /* Bit 1 */

#define DMA_CFGR1_MSIZE                         ((uint16_t)0x0C00) /* MSIZE[1:0] bits (Memory size) */
#define DMA_CFGR1_MSIZE_0                       ((uint16_t)0x0400) /* Bit 0 */
#define DMA_CFGR1_MSIZE_1                       ((uint16_t)0x0800) /* Bit 1 */

#define DMA_CFGR1_PL                            ((uint16_t)0x3000) /* PL[1:0] bits(Channel Priority level) */
#define DMA_CFGR1_PL_0                          ((uint16_t)0x1000) /* Bit 0 */
#define DMA_CFGR1_PL_1                          ((uint16_t)0x2000) /* Bit 1 */

#define DMA_CFGR1_MEM2MEM                       ((uint16_t)0x4000) /* Memory to memory mode */

/*******************  Bit definition for DMA_CFGR2 register  *******************/
#define DMA_CFGR2_EN                            ((uint16_t)0x0001) /* Channel enable */
#define DMA_CFGR2_TCIE                          ((uint16_t)0x0002) /* Transfer complete interrupt enable */
#define DMA_CFGR2_HTIE                          ((uint16_t)0x0004) /* Half Transfer interrupt enable */
#define DMA_CFGR2_TEIE                          ((uint16_t)0x0008) /* Transfer error interrupt enable */
#define DMA_CFGR2_DIR                           ((uint16_t)0x0010) /* Data transfer direction */
#define DMA_CFGR2_CIRC                          ((uint16_t)0x0020) /* Circular mode */
#define DMA_CFGR2_PINC                          ((uint16_t)0x0040) /* Peripheral increment mode */
#define DMA_CFGR2_MINC                          ((uint16_t)0x0080) /* Memory increment mode */

#define DMA_CFGR2_PSIZE                         ((uint16_t)0x0300) /* PSIZE[1:0] bits (Peripheral size) */
#define DMA_CFGR2_PSIZE_0                       ((uint16_t)0x0100) /* Bit 0 */
#define DMA_CFGR2_PSIZE_1                       ((uint16_t)0x0200) /* Bit 1 */

#define DMA_CFGR2_MSIZE                         ((uint16_t)0x0C00) /* MSIZE[1:0] bits (Memory size) */
#define DMA_CFGR2_MSIZE_0                       ((uint16_t)0x0400) /* Bit 0 */
#define DMA_CFGR2_MSIZE_1                       ((uint16_t)0x0800) /* Bit 1 */

#define DMA_CFGR2_PL                            ((uint16_t)0x3000) /* PL[1:0] bits (Channel Priority level) */
#define DMA_CFGR2_PL_0                          ((uint16_t)0x1000) /* Bit 0 */
#define DMA_CFGR2_PL_1                          ((uint16_t)0x2000) /* Bit 1 */

#define DMA_CFGR2_MEM2MEM                       ((uint16_t)0x4000) /* Memory to memory mode */

/*******************  Bit definition for DMA_CFGR3 register  *******************/
#define DMA_CFGR3_EN                            ((uint16_t)0x0001) /* Channel enable */
#define DMA_CFGR3_TCIE                          ((uint16_t)0x0002) /* Transfer complete interrupt enable */
#define DMA_CFGR3_HTIE                          ((uint16_t)0x0004) /* Half Transfer interrupt enable */
#define DMA_CFGR3_TEIE                          ((uint16_t)0x0008) /* Transfer error interrupt enable */
#define DMA_CFGR3_DIR                           ((uint16_t)0x0010) /* Data transfer direction */
#define DMA_CFGR3_CIRC                          ((uint16_t)0x0020) /* Circular mode */
#define DMA_CFGR3_PINC                          ((uint16_t)0x0040) /* Peripheral increment mode */
#define DMA_CFGR3_MINC                          ((uint16_t)0x0080) /* Memory increment mode */

#define DMA_CFGR3_PSIZE                         ((uint16_t)0x0300) /* PSIZE[1:0] bits (Peripheral size) */
#define DMA_CFGR3_PSIZE_0                       ((uint16_t)0x0100) /* Bit 0 */
#define DMA_CFGR3_PSIZE_1                       ((uint16_t)0x0200) /* Bit 1 */

#define DMA_CFGR3_MSIZE                         ((uint16_t)0x0C00) /* MSIZE[1:0] bits (Memory size) */
#define DMA_CFGR3_MSIZE_0                       ((uint16_t)0x0400) /* Bit 0 */
#define DMA_CFGR3_MSIZE_1                       ((uint16_t)0x0800) /* Bit 1 */

#define DMA_CFGR3_PL                            ((uint16_t)0x3000) /* PL[1:0] bits (Channel Priority level) */
#define DMA_CFGR3_PL_0                          ((uint16_t)0x1000) /* Bit 0 */
#define DMA_CFGR3_PL_1                          ((uint16_t)0x2000) /* Bit 1 */

#define DMA_CFGR3_MEM2MEM                       ((uint16_t)0x4000) /* Memory to memory mode */

/*******************  Bit definition for DMA_CFG4 register  *******************/
#define DMA_CFG4_EN                             ((uint16_t)0x0001) /* Channel enable */
#define DMA_CFG4_TCIE                           ((uint16_t)0x0002) /* Transfer complete interrupt enable */
#define DMA_CFG4_HTIE                           ((uint16_t)0x0004) /* Half Transfer interrupt enable */
#define DMA_CFG4_TEIE                           ((uint16_t)0x0008) /* Transfer error interrupt enable */
#define DMA_CFG4_DIR                            ((uint16_t)0x0010) /* Data transfer direction */
#define DMA_CFG4_CIRC                           ((uint16_t)0x0020) /* Circular mode */
#define DMA_CFG4_PINC                           ((uint16_t)0x0040) /* Peripheral increment mode */
#define DMA_CFG4_MINC                           ((uint16_t)0x0080) /* Memory increment mode */

#define DMA_CFG4_PSIZE                          ((uint16_t)0x0300) /* PSIZE[1:0] bits (Peripheral size) */
#define DMA_CFG4_PSIZE_0                        ((uint16_t)0x0100) /* Bit 0 */
#define DMA_CFG4_PSIZE_1                        ((uint16_t)0x0200) /* Bit 1 */

#define DMA_CFG4_MSIZE                          ((uint16_t)0x0C00) /* MSIZE[1:0] bits (Memory size) */
#define DMA_CFG4_MSIZE_0                        ((uint16_t)0x0400) /* Bit 0 */
#define DMA_CFG4_MSIZE_1                        ((uint16_t)0x0800) /* Bit 1 */

#define DMA_CFG4_PL                             ((uint16_t)0x3000) /* PL[1:0] bits (Channel Priority level) */
#define DMA_CFG4_PL_0                           ((uint16_t)0x1000) /* Bit 0 */
#define DMA_CFG4_PL_1                           ((uint16_t)0x2000) /* Bit 1 */

#define DMA_CFG4_MEM2MEM                        ((uint16_t)0x4000) /* Memory to memory mode */

/******************  Bit definition for DMA_CFG5 register  *******************/
#define DMA_CFG5_EN                             ((uint16_t)0x0001) /* Channel enable */
#define DMA_CFG5_TCIE                           ((uint16_t)0x0002) /* Transfer complete interrupt enable */
#define DMA_CFG5_HTIE                           ((uint16_t)0x0004) /* Half Transfer interrupt enable */
#define DMA_CFG5_TEIE                           ((uint16_t)0x0008) /* Transfer error interrupt enable */
#define DMA_CFG5_DIR                            ((uint16_t)0x0010) /* Data transfer direction */
#define DMA_CFG5_CIRC                           ((uint16_t)0x0020) /* Circular mode */
#define DMA_CFG5_PINC                           ((uint16_t)0x0040) /* Peripheral increment mode */
#define DMA_CFG5_MINC                           ((uint16_t)0x0080) /* Memory increment mode */

#define DMA_CFG5_PSIZE                          ((uint16_t)0x0300) /* PSIZE[1:0] bits (Peripheral size) */
#define DMA_CFG5_PSIZE_0                        ((uint16_t)0x0100) /* Bit 0 */
#define DMA_CFG5_PSIZE_1                        ((uint16_t)0x0200) /* Bit 1 */

#define DMA_CFG5_MSIZE                          ((uint16_t)0x0C00) /* MSIZE[1:0] bits (Memory size) */
#define DMA_CFG5_MSIZE_0                        ((uint16_t)0x0400) /* Bit 0 */
#define DMA_CFG5_MSIZE_1                        ((uint16_t)0x0800) /* Bit 1 */

#define DMA_CFG5_PL                             ((uint16_t)0x3000) /* PL[1:0] bits (Channel Priority level) */
#define DMA_CFG5_PL_0                           ((uint16_t)0x1000) /* Bit 0 */
#define DMA_CFG5_PL_1                           ((uint16_t)0x2000) /* Bit 1 */

#define DMA_CFG5_MEM2MEM                        ((uint16_t)0x4000) /* Memory to memory mode enable */

/*******************  Bit definition for DMA_CFG6 register  *******************/
#define DMA_CFG6_EN                             ((uint16_t)0x0001) /* Channel enable */
#define DMA_CFG6_TCIE                           ((uint16_t)0x0002) /* Transfer complete interrupt enable */
#define DMA_CFG6_HTIE                           ((uint16_t)0x0004) /* Half Transfer interrupt enable */
#define DMA_CFG6_TEIE                           ((uint16_t)0x0008) /* Transfer error interrupt enable */
#define DMA_CFG6_DIR                            ((uint16_t)0x0010) /* Data transfer direction */
#define DMA_CFG6_CIRC                           ((uint16_t)0x0020) /* Circular mode */
#define DMA_CFG6_PINC                           ((uint16_t)0x0040) /* Peripheral increment mode */
#define DMA_CFG6_MINC                           ((uint16_t)0x0080) /* Memory increment mode */

#define DMA_CFG6_PSIZE                          ((uint16_t)0x0300) /* PSIZE[1:0] bits (Peripheral size) */
#define DMA_CFG6_PSIZE_0                        ((uint16_t)0x0100) /* Bit 0 */
#define DMA_CFG6_PSIZE_1                        ((uint16_t)0x0200) /* Bit 1 */

#define DMA_CFG6_MSIZE                          ((uint16_t)0x0C00) /* MSIZE[1:0] bits (Memory size) */
#define DMA_CFG6_MSIZE_0                        ((uint16_t)0x0400) /* Bit 0 */
#define DMA_CFG6_MSIZE_1                        ((uint16_t)0x0800) /* Bit 1 */

#define DMA_CFG6_PL                             ((uint16_t)0x3000) /* PL[1:0] bits (Channel Priority level) */
#define DMA_CFG6_PL_0                           ((uint16_t)0x1000) /* Bit 0 */
#define DMA_CFG6_PL_1                           ((uint16_t)0x2000) /* Bit 1 */

#define DMA_CFG6_MEM2MEM                        ((uint16_t)0x4000) /* Memory to memory mode */

/*******************  Bit definition for DMA_CFG7 register  *******************/
#define DMA_CFG7_EN                             ((uint16_t)0x0001) /* Channel enable */
#define DMA_CFG7_TCIE                           ((uint16_t)0x0002) /* Transfer complete interrupt enable */
#define DMA_CFG7_HTIE                           ((uint16_t)0x0004) /* Half Transfer interrupt enable */
#define DMA_CFG7_TEIE                           ((uint16_t)0x0008) /* Transfer error interrupt enable */
#define DMA_CFG7_DIR                            ((uint16_t)0x0010) /* Data transfer direction */
#define DMA_CFG7_CIRC                           ((uint16_t)0x0020) /* Circular mode */
#define DMA_CFG7_PINC                           ((uint16_t)0x0040) /* Peripheral increment mode */
#define DMA_CFG7_MINC                           ((uint16_t)0x0080) /* Memory increment mode */

#define DMA_CFG7_PSIZE                          ((uint16_t)0x0300) /* PSIZE[1:0] bits (Peripheral size) */
#define DMA_CFG7_PSIZE_0                        ((uint16_t)0x0100) /* Bit 0 */
#define DMA_CFG7_PSIZE_1                        ((uint16_t)0x0200) /* Bit 1 */

#define DMA_CFG7_MSIZE                          ((uint16_t)0x0C00) /* MSIZE[1:0] bits (Memory size) */
#define DMA_CFG7_MSIZE_0                        ((uint16_t)0x0400) /* Bit 0 */
#define DMA_CFG7_MSIZE_1                        ((uint16_t)0x0800) /* Bit 1 */

#define DMA_CFG7_PL                             ((uint16_t)0x3000) /* PL[1:0] bits (Channel Priority level) */
#define DMA_CFG7_PL_0                           ((uint16_t)0x1000) /* Bit 0 */
#define DMA_CFG7_PL_1                           ((uint16_t)0x2000) /* Bit 1 */

#define DMA_CFG7_MEM2MEM                        ((uint16_t)0x4000) /* Memory to memory mode enable */

/******************  Bit definition for DMA_CNTR1 register  ******************/
#define DMA_CNTR1_NDT                           ((uint16_t)0xFFFF) /* Number of data to Transfer */

/******************  Bit definition for DMA_CNTR2 register  ******************/
#define DMA_CNTR2_NDT                           ((uint16_t)0xFFFF) /* Number of data to Transfer */

/******************  Bit definition for DMA_CNTR3 register  ******************/
#define DMA_CNTR3_NDT                           ((uint16_t)0xFFFF) /* Number of data to Transfer */

/******************  Bit definition for DMA_CNTR4 register  ******************/
#define DMA_CNTR4_NDT                           ((uint16_t)0xFFFF) /* Number of data to Transfer */

/******************  Bit definition for DMA_CNTR5 register  ******************/
#define DMA_CNTR5_NDT                           ((uint16_t)0xFFFF) /* Number of data to Transfer */

/******************  Bit definition for DMA_CNTR6 register  ******************/
#define DMA_CNTR6_NDT                           ((uint16_t)0xFFFF) /* Number of data to Transfer */

/******************  Bit definition for DMA_CNTR7 register  ******************/
#define DMA_CNTR7_NDT                           ((uint16_t)0xFFFF) /* Number of data to Transfer */

/******************  Bit definition for DMA_PADDR1 register  *******************/
#define DMA_PADDR1_PA                           ((uint32_t)0xFFFFFFFF) /* Peripheral Address */

/******************  Bit definition for DMA_PADDR2 register  *******************/
#define DMA_PADDR2_PA                           ((uint32_t)0xFFFFFFFF) /* Peripheral Address */

/******************  Bit definition for DMA_PADDR3 register  *******************/
#define DMA_PADDR3_PA                           ((uint32_t)0xFFFFFFFF) /* Peripheral Address */

/******************  Bit definition for DMA_PADDR4 register  *******************/
#define DMA_PADDR4_PA                           ((uint32_t)0xFFFFFFFF) /* Peripheral Address */

/******************  Bit definition for DMA_PADDR5 register  *******************/
#define DMA_PADDR5_PA                           ((uint32_t)0xFFFFFFFF) /* Peripheral Address */

/******************  Bit definition for DMA_PADDR6 register  *******************/
#define DMA_PADDR6_PA                           ((uint32_t)0xFFFFFFFF) /* Peripheral Address */

/******************  Bit definition for DMA_PADDR7 register  *******************/
#define DMA_PADDR7_PA                           ((uint32_t)0xFFFFFFFF) /* Peripheral Address */

/******************  Bit definition for DMA_MADDR1 register  *******************/
#define DMA_MADDR1_MA                           ((uint32_t)0xFFFFFFFF) /* Memory Address */

/******************  Bit definition for DMA_MADDR2 register  *******************/
#define DMA_MADDR2_MA                           ((uint32_t)0xFFFFFFFF) /* Memory Address */

/******************  Bit definition for DMA_MADDR3 register  *******************/
#define DMA_MADDR3_MA                           ((uint32_t)0xFFFFFFFF) /* Memory Address */

/******************  Bit definition for DMA_MADDR4 register  *******************/
#define DMA_MADDR4_MA                           ((uint32_t)0xFFFFFFFF) /* Memory Address */

/******************  Bit definition for DMA_MADDR5 register  *******************/
#define DMA_MADDR5_MA                           ((uint32_t)0xFFFFFFFF) /* Memory Address */

/******************  Bit definition for DMA_MADDR6 register  *******************/
#define DMA_MADDR6_MA                           ((uint32_t)0xFFFFFFFF) /* Memory Address */

/******************  Bit definition for DMA_MADDR7 register  *******************/
#define DMA_MADDR7_MA                           ((uint32_t)0xFFFFFFFF) /* Memory Address */

/******************************************************************************/
/*                    External Interrupt/Event Controller                     */
/******************************************************************************/

/*******************  Bit definition for EXTI_INTENR register  *******************/
#define EXTI_INTENR_MR0                         ((uint32_t)0x00000001) /* Interrupt Mask on line 0 */
#define EXTI_INTENR_MR1                         ((uint32_t)0x00000002) /* Interrupt Mask on line 1 */
#define EXTI_INTENR_MR2                         ((uint32_t)0x00000004) /* Interrupt Mask on line 2 */
#define EXTI_INTENR_MR3                         ((uint32_t)0x00000008) /* Interrupt Mask on line 3 */
#define EXTI_INTENR_MR4                         ((uint32_t)0x00000010) /* Interrupt Mask on line 4 */
#define EXTI_INTENR_MR5                         ((uint32_t)0x00000020) /* Interrupt Mask on line 5 */
#define EXTI_INTENR_MR6                         ((uint32_t)0x00000040) /* Interrupt Mask on line 6 */
#define EXTI_INTENR_MR7                         ((uint32_t)0x00000080) /* Interrupt Mask on line 7 */
#define EXTI_INTENR_MR8                         ((uint32_t)0x00000100) /* Interrupt Mask on line 8 */
#define EXTI_INTENR_MR9                         ((uint32_t)0x00000200) /* Interrupt Mask on line 9 */

/*******************  Bit definition for EXTI_EVENR register  *******************/
#define EXTI_EVENR_MR0                          ((uint32_t)0x00000001) /* Event Mask on line 0 */
#define EXTI_EVENR_MR1                          ((uint32_t)0x00000002) /* Event Mask on line 1 */
#define EXTI_EVENR_MR2                          ((uint32_t)0x00000004) /* Event Mask on line 2 */
#define EXTI_EVENR_MR3                          ((uint32_t)0x00000008) /* Event Mask on line 3 */
#define EXTI_EVENR_MR4                          ((uint32_t)0x00000010) /* Event Mask on line 4 */
#define EXTI_EVENR_MR5                          ((uint32_t)0x00000020) /* Event Mask on line 5 */
#define EXTI_EVENR_MR6                          ((uint32_t)0x00000040) /* Event Mask on line 6 */
#define EXTI_EVENR_MR7                          ((uint32_t)0x00000080) /* Event Mask on line 7 */
#define EXTI_EVENR_MR8                          ((uint32_t)0x00000100) /* Event Mask on line 8 */
#define EXTI_EVENR_MR9                          ((uint32_t)0x00000200) /* Event Mask on line 9 */

/******************  Bit definition for EXTI_RTENR register  *******************/
#define EXTI_RTENR_TR0                          ((uint32_t)0x00000001) /* Rising trigger event configuration bit of line 0 */
#define EXTI_RTENR_TR1                          ((uint32_t)0x00000002) /* Rising trigger event configuration bit of line 1 */
#define EXTI_RTENR_TR2                          ((uint32_t)0x00000004) /* Rising trigger event configuration bit of line 2 */
#define EXTI_RTENR_TR3                          ((uint32_t)0x00000008) /* Rising trigger event configuration bit of line 3 */
#define EXTI_RTENR_TR4                          ((uint32_t)0x00000010) /* Rising trigger event configuration bit of line 4 */
#define EXTI_RTENR_TR5                          ((uint32_t)0x00000020) /* Rising trigger event configuration bit of line 5 */
#define EXTI_RTENR_TR6                          ((uint32_t)0x00000040) /* Rising trigger event configuration bit of line 6 */
#define EXTI_RTENR_TR7                          ((uint32_t)0x00000080) /* Rising trigger event configuration bit of line 7 */
#define EXTI_RTENR_TR8                          ((uint32_t)0x00000100) /* Rising trigger event configuration bit of line 8 */
#define EXTI_RTENR_TR9                          ((uint32_t)0x00000200) /* Rising trigger event configuration bit of line 9 */

/******************  Bit definition for EXTI_FTENR register  *******************/
#define EXTI_FTENR_TR0                          ((uint32_t)0x00000001) /* Falling trigger event configuration bit of line 0 */
#define EXTI_FTENR_TR1                          ((uint32_t)0x00000002) /* Falling trigger event configuration bit of line 1 */
#define EXTI_FTENR_TR2                          ((uint32_t)0x00000004) /* Falling trigger event configuration bit of line 2 */
#define EXTI_FTENR_TR3                          ((uint32_t)0x00000008) /* Falling trigger event configuration bit of line 3 */
#define EXTI_FTENR_TR4                          ((uint32_t)0x00000010) /* Falling trigger event configuration bit of line 4 */
#define EXTI_FTENR_TR5                          ((uint32_t)0x00000020) /* Falling trigger event configuration bit of line 5 */
#define EXTI_FTENR_TR6                          ((uint32_t)0x00000040) /* Falling trigger event configuration bit of line 6 */
#define EXTI_FTENR_TR7                          ((uint32_t)0x00000080) /* Falling trigger event configuration bit of line 7 */
#define EXTI_FTENR_TR8                          ((uint32_t)0x00000100) /* Falling trigger event configuration bit of line 8 */
#define EXTI_FTENR_TR9                          ((uint32_t)0x00000200) /* Falling trigger event configuration bit of line 9 */

/******************  Bit definition for EXTI_SWIEVR register  ******************/
#define EXTI_SWIEVR_SWIEVR0                     ((uint32_t)0x00000001) /* Software Interrupt on line 0 */
#define EXTI_SWIEVR_SWIEVR1                     ((uint32_t)0x00000002) /* Software Interrupt on line 1 */
#define EXTI_SWIEVR_SWIEVR2                     ((uint32_t)0x00000004) /* Software Interrupt on line 2 */
#define EXTI_SWIEVR_SWIEVR3                     ((uint32_t)0x00000008) /* Software Interrupt on line 3 */
#define EXTI_SWIEVR_SWIEVR4                     ((uint32_t)0x00000010) /* Software Interrupt on line 4 */
#define EXTI_SWIEVR_SWIEVR5                     ((uint32_t)0x00000020) /* Software Interrupt on line 5 */
#define EXTI_SWIEVR_SWIEVR6                     ((uint32_t)0x00000040) /* Software Interrupt on line 6 */
#define EXTI_SWIEVR_SWIEVR7                     ((uint32_t)0x00000080) /* Software Interrupt on line 7 */
#define EXTI_SWIEVR_SWIEVR8                     ((uint32_t)0x00000100) /* Software Interrupt on line 8 */
#define EXTI_SWIEVR_SWIEVR9                     ((uint32_t)0x00000200) /* Software Interrupt on line 9 */

/*******************  Bit definition for EXTI_INTFR register  ********************/
#define EXTI_INTF_INTF0                         ((uint32_t)0x00000001) /* Pending bit for line 0 */
#define EXTI_INTF_INTF1                         ((uint32_t)0x00000002) /* Pending bit for line 1 */
#define EXTI_INTF_INTF2                         ((uint32_t)0x00000004) /* Pending bit for line 2 */
#define EXTI_INTF_INTF3                         ((uint32_t)0x00000008) /* Pending bit for line 3 */
#define EXTI_INTF_INTF4                         ((uint32_t)0x00000010) /* Pending bit for line 4 */
#define EXTI_INTF_INTF5                         ((uint32_t)0x00000020) /* Pending bit for line 5 */
#define EXTI_INTF_INTF6                         ((uint32_t)0x00000040) /* Pending bit for line 6 */
#define EXTI_INTF_INTF7                         ((uint32_t)0x00000080) /* Pending bit for line 7 */
#define EXTI_INTF_INTF8                         ((uint32_t)0x00000100) /* Pending bit for line 8 */
#define EXTI_INTF_INTF9                         ((uint32_t)0x00000200) /* Pending bit for line 9 */

/******************************************************************************/
/*                      FLASH and Option Bytes Registers                      */
/******************************************************************************/

/*******************  Bit definition for FLASH_ACTLR register  ******************/
#define FLASH_ACTLR_LATENCY                     ((uint8_t)0x03) /* LATENCY[2:0] bits (Latency) */
#define FLASH_ACTLR_LATENCY_0                   ((uint8_t)0x00) /* Bit 0 */
#define FLASH_ACTLR_LATENCY_1                   ((uint8_t)0x01) /* Bit 0 */
#define FLASH_ACTLR_LATENCY_2                   ((uint8_t)0x02) /* Bit 1 */

/******************  Bit definition for FLASH_KEYR register  ******************/
#define FLASH_KEYR_FKEYR                        ((uint32_t)0xFFFFFFFF) /* FPEC Key */

/*****************  Bit definition for FLASH_OBKEYR register  ****************/
#define FLASH_OBKEYR_OBKEYR                     ((uint32_t)0xFFFFFFFF) /* Option Byte Key */

/******************  Bit definition for FLASH_STATR register  *******************/
#define FLASH_STATR_BSY                         ((uint32_t)0x00000001) /* Busy */
#define FLASH_STATR_WRPRTERR                    ((uint32_t)0x00000010) /* Write Protection Error */
#define FLASH_STATR_EOP                         ((uint32_t)0x00000020) /* End of operation */
#define FLASH_STATR_MODE                        ((uint32_t)0x00004000) /* User area and BOOT area */
#define FLASH_STATR_LOCK                        ((uint32_t)0x00008000) /* BOOT Lock */

/*******************  Bit definition for FLASH_CTLR register  *******************/
#define FLASH_CTLR_PG                           ((uint32_t)0x00000001)     /* Programming */
#define FLASH_CTLR_PER                          ((uint32_t)0x00000002)     /* Page Erase 1KByte*/
#define FLASH_CTLR_MER                          ((uint32_t)0x00000004)     /* Mass Erase */
#define FLASH_CTLR_OPTPG                        ((uint32_t)0x00000010)     /* Option Byte Programming */
#define FLASH_CTLR_OPTER                        ((uint32_t)0x00000020)     /* Option Byte Erase */
#define FLASH_CTLR_STRT                         ((uint32_t)0x00000040)     /* Start */
#define FLASH_CTLR_LOCK                         ((uint32_t)0x00000080)     /* Lock */
#define FLASH_CTLR_OPTWRE                       ((uint32_t)0x00000200)     /* Option Bytes Write Enable */
#define FLASH_CTLR_ERRIE                        ((uint32_t)0x00000400)     /* Error Interrupt Enable */
#define FLASH_CTLR_EOPIE                        ((uint32_t)0x00001000)     /* End of operation interrupt enable */
#define FLASH_CTLR_FLOCK                        ((uint32_t)0x00008000) /* Fast programming lock */
#define FLASH_CTLR_PAGE_PG                      ((uint32_t)0x00010000) /* Page Programming 64Byte */
#define FLASH_CTLR_PAGE_ER                      ((uint32_t)0x00020000) /* Page Erase 64Byte */
#define FLASH_CTLR_BUF_LOAD                     ((uint32_t)0x00040000) /* Buffer Load */
#define FLASH_CTLR_BUF_RST                      ((uint32_t)0x00080000) /* Buffer Reset */

/*******************  Bit definition for FLASH_ADDR register  *******************/
#define FLASH_ADDR_FAR                          ((uint32_t)0xFFFFFFFF) /* Flash Address */

/******************  Bit definition for FLASH_OBR register  *******************/
#define FLASH_OBR_OPTERR                        ((uint32_t)0x00000001) /* Option Byte Error */
#define FLASH_OBR_RDPRT                         ((uint32_t)0x00000002) /* Read protection */

#define FLASH_OBR_USER                          ((uint32_t)0x000003FC) /* User Option Bytes */
#define FLASH_OBR_WDG_SW                        ((uint32_t)0x00000004) /* WDG_SW */
// #define FLASH_OBR_nRST_STOP                     ((uint32_t)0x00000008) /* nRST_STOP */
#define FLASH_OBR_nRST_STDBY                    ((uint32_t)0x00000010) /* nRST_STDBY */
#define FLASH_OBR_RST_MODE                      ((uint32_t)0x00000060) /* RST_MODE */
#define FLASH_OBR_STATR_MODE                    ((uint32_t)0x00000080) /* STATR_MODE */
#define FLASH_OBR_DATA0                         ((uint32_t)0x0003FC00) /* DATA0 */
#define FLASH_OBR_DATA1                         ((uint32_t)0x03FC0000) /* DATA1 */

/******************  Bit definition for FLASH_WPR register  ******************/
#define FLASH_WPR_WRP                           ((uint32_t)0xFFFFFFFF) /* Write Protect */

/******************  Bit definition for OB_RDPR register  *******************/
#define OB_RDPR_RDPR                         ((uint16_t)0x00FF) /* Read protection option byte */
#define OB_RDPR_nRDPR                        ((uint16_t)0xFF00) /* Read protection complemented option byte */

/******************  Bit definition for OB_USER register  ******************/
#define OB_USER_USER                         ((uint16_t)0x00FF) /* User option byte */
#define OB_USER_nUSER                        ((uint16_t)0xFF00) /* User complemented option byte */

#define OB_USER_WDG_SW                        ((uint16_t)0x00000001) /* WDG_SW */
// #define OB_USER_nRST_STOP                     ((uint16_t)0x00000002) /* nRST_STOP */
#define OB_USER_nRST_STDBY                    ((uint16_t)0x00000004) /* nRST_STDBY */
#define OB_USER_RST_MODE_0                    ((uint16_t)0x00000008) /* RST_MODE */
#define OB_USER_RST_MODE_1                    ((uint16_t)0x00000010) /* RST_MODE */
#define OB_USER_STATR_MODE                    ((uint16_t)0x00000020) /* STATR_MODE */

#define OB_USER_RST_MODE_128U                 ((uint16_t)0x00000000) /* RST_MODE */
#define OB_USER_RST_MODE_1M                   ((uint16_t)0x00000008) /* RST_MODE */
#define OB_USER_RST_MODE_12M                  ((uint16_t)0x00000010) /* RST_MODE */
#define OB_USER_RST_MODE_NONE                 ((uint16_t)0x00000018) /* RST_MODE */

/******************  Bit definition for OB_Data0 register  *****************/
#define OB_Data0_Data0                       ((uint16_t)0x00FF) /* User data storage option byte */
#define OB_Data0_nData0                      ((uint16_t)0xFF00) /* User data storage complemented option byte */

/******************  Bit definition for OB_Data1 register  *****************/
#define OB_Data1_Data1                       ((uint16_t)0x00FF) /* User data storage option byte */
#define OB_Data1_nData1                      ((uint16_t)0xFF00) /* User data storage complemented option byte */

/******************  Bit definition for OB_WRPR0 register  ******************/
#define OB_WRPR0_WRPR0                       ((uint16_t)0x00FF) /* Flash memory write protection option bytes */
#define OB_WRPR0_nWRPR0                      ((uint16_t)0xFF00) /* Flash memory write protection complemented option bytes */

/******************  Bit definition for OB_WRPR1 register  ******************/
#define OB_WRPR1_WRPR1                       ((uint16_t)0x00FF) /* Flash memory write protection option bytes */
#define OB_WRPR1_nWRPR1                      ((uint16_t)0xFF00) /* Flash memory write protection complemented option bytes */


/******************************************************************************/
/*                General Purpose and Alternate Function I/O                  */
/******************************************************************************/

/*******************  Bit definition for GPIO_CFGLR register  *******************/
#define GPIO_CFGLR_MODE                         ((uint32_t)0x33333333) /* Port x mode bits */

#define GPIO_CFGLR_MODE0                        ((uint32_t)0x00000003) /* MODE0[1:0] bits (Port x mode bits, pin 0) */
#define GPIO_CFGLR_MODE0_0                      ((uint32_t)0x00000001) /* Bit 0 */
#define GPIO_CFGLR_MODE0_1                      ((uint32_t)0x00000002) /* Bit 1 */

#define GPIO_CFGLR_MODE1                        ((uint32_t)0x00000030) /* MODE1[1:0] bits (Port x mode bits, pin 1) */
#define GPIO_CFGLR_MODE1_0                      ((uint32_t)0x00000010) /* Bit 0 */
#define GPIO_CFGLR_MODE1_1                      ((uint32_t)0x00000020) /* Bit 1 */

#define GPIO_CFGLR_MODE2                        ((uint32_t)0x00000300) /* MODE2[1:0] bits (Port x mode bits, pin 2) */
#define GPIO_CFGLR_MODE2_0                      ((uint32_t)0x00000100) /* Bit 0 */
#define GPIO_CFGLR_MODE2_1                      ((uint32_t)0x00000200) /* Bit 1 */

#define GPIO_CFGLR_MODE3                        ((uint32_t)0x00003000) /* MODE3[1:0] bits (Port x mode bits, pin 3) */
#define GPIO_CFGLR_MODE3_0                      ((uint32_t)0x00001000) /* Bit 0 */
#define GPIO_CFGLR_MODE3_1                      ((uint32_t)0x00002000) /* Bit 1 */

#define GPIO_CFGLR_MODE4                        ((uint32_t)0x00030000) /* MODE4[1:0] bits (Port x mode bits, pin 4) */
#define GPIO_CFGLR_MODE4_0                      ((uint32_t)0x00010000) /* Bit 0 */
#define GPIO_CFGLR_MODE4_1                      ((uint32_t)0x00020000) /* Bit 1 */

#define GPIO_CFGLR_MODE5                        ((uint32_t)0x00300000) /* MODE5[1:0] bits (Port x mode bits, pin 5) */
#define GPIO_CFGLR_MODE5_0                      ((uint32_t)0x00100000) /* Bit 0 */
#define GPIO_CFGLR_MODE5_1                      ((uint32_t)0x00200000) /* Bit 1 */

#define GPIO_CFGLR_MODE6                        ((uint32_t)0x03000000) /* MODE6[1:0] bits (Port x mode bits, pin 6) */
#define GPIO_CFGLR_MODE6_0                      ((uint32_t)0x01000000) /* Bit 0 */
#define GPIO_CFGLR_MODE6_1                      ((uint32_t)0x02000000) /* Bit 1 */

#define GPIO_CFGLR_MODE7                        ((uint32_t)0x30000000) /* MODE7[1:0] bits (Port x mode bits, pin 7) */
#define GPIO_CFGLR_MODE7_0                      ((uint32_t)0x10000000) /* Bit 0 */
#define GPIO_CFGLR_MODE7_1                      ((uint32_t)0x20000000) /* Bit 1 */

#define GPIO_CFGLR_CNF                          ((uint32_t)0xCCCCCCCC) /* Port x configuration bits */

#define GPIO_CFGLR_CNF0                         ((uint32_t)0x0000000C) /* CNF0[1:0] bits (Port x configuration bits, pin 0) */
#define GPIO_CFGLR_CNF0_0                       ((uint32_t)0x00000004) /* Bit 0 */
#define GPIO_CFGLR_CNF0_1                       ((uint32_t)0x00000008) /* Bit 1 */

#define GPIO_CFGLR_CNF1                         ((uint32_t)0x000000C0) /* CNF1[1:0] bits (Port x configuration bits, pin 1) */
#define GPIO_CFGLR_CNF1_0                       ((uint32_t)0x00000040) /* Bit 0 */
#define GPIO_CFGLR_CNF1_1                       ((uint32_t)0x00000080) /* Bit 1 */

#define GPIO_CFGLR_CNF2                         ((uint32_t)0x00000C00) /* CNF2[1:0] bits (Port x configuration bits, pin 2) */
#define GPIO_CFGLR_CNF2_0                       ((uint32_t)0x00000400) /* Bit 0 */
#define GPIO_CFGLR_CNF2_1                       ((uint32_t)0x00000800) /* Bit 1 */

#define GPIO_CFGLR_CNF3                         ((uint32_t)0x0000C000) /* CNF3[1:0] bits (Port x configuration bits, pin 3) */
#define GPIO_CFGLR_CNF3_0                       ((uint32_t)0x00004000) /* Bit 0 */
#define GPIO_CFGLR_CNF3_1                       ((uint32_t)0x00008000) /* Bit 1 */

#define GPIO_CFGLR_CNF4                         ((uint32_t)0x000C0000) /* CNF4[1:0] bits (Port x configuration bits, pin 4) */
#define GPIO_CFGLR_CNF4_0                       ((uint32_t)0x00040000) /* Bit 0 */
#define GPIO_CFGLR_CNF4_1                       ((uint32_t)0x00080000) /* Bit 1 */

#define GPIO_CFGLR_CNF5                         ((uint32_t)0x00C00000) /* CNF5[1:0] bits (Port x configuration bits, pin 5) */
#define GPIO_CFGLR_CNF5_0                       ((uint32_t)0x00400000) /* Bit 0 */
#define GPIO_CFGLR_CNF5_1                       ((uint32_t)0x00800000) /* Bit 1 */

#define GPIO_CFGLR_CNF6                         ((uint32_t)0x0C000000) /* CNF6[1:0] bits (Port x configuration bits, pin 6) */
#define GPIO_CFGLR_CNF6_0                       ((uint32_t)0x04000000) /* Bit 0 */
#define GPIO_CFGLR_CNF6_1                       ((uint32_t)0x08000000) /* Bit 1 */

#define GPIO_CFGLR_CNF7                         ((uint32_t)0xC0000000) /* CNF7[1:0] bits (Port x configuration bits, pin 7) */
#define GPIO_CFGLR_CNF7_0                       ((uint32_t)0x40000000) /* Bit 0 */
#define GPIO_CFGLR_CNF7_1                       ((uint32_t)0x80000000) /* Bit 1 */

/*******************  Bit definition for GPIO_CFGHR register  *******************/
#define GPIO_CFGHR_MODE                         ((uint32_t)0x33333333) /* Port x mode bits */

#define GPIO_CFGHR_MODE8                        ((uint32_t)0x00000003) /* MODE8[1:0] bits (Port x mode bits, pin 8) */
#define GPIO_CFGHR_MODE8_0                      ((uint32_t)0x00000001) /* Bit 0 */
#define GPIO_CFGHR_MODE8_1                      ((uint32_t)0x00000002) /* Bit 1 */

#define GPIO_CFGHR_MODE9                        ((uint32_t)0x00000030) /* MODE9[1:0] bits (Port x mode bits, pin 9) */
#define GPIO_CFGHR_MODE9_0                      ((uint32_t)0x00000010) /* Bit 0 */
#define GPIO_CFGHR_MODE9_1                      ((uint32_t)0x00000020) /* Bit 1 */

#define GPIO_CFGHR_MODE10                       ((uint32_t)0x00000300) /* MODE10[1:0] bits (Port x mode bits, pin 10) */
#define GPIO_CFGHR_MODE10_0                     ((uint32_t)0x00000100) /* Bit 0 */
#define GPIO_CFGHR_MODE10_1                     ((uint32_t)0x00000200) /* Bit 1 */

#define GPIO_CFGHR_MODE11                       ((uint32_t)0x00003000) /* MODE11[1:0] bits (Port x mode bits, pin 11) */
#define GPIO_CFGHR_MODE11_0                     ((uint32_t)0x00001000) /* Bit 0 */
#define GPIO_CFGHR_MODE11_1                     ((uint32_t)0x00002000) /* Bit 1 */

#define GPIO_CFGHR_MODE12                       ((uint32_t)0x00030000) /* MODE12[1:0] bits (Port x mode bits, pin 12) */
#define GPIO_CFGHR_MODE12_0                     ((uint32_t)0x00010000) /* Bit 0 */
#define GPIO_CFGHR_MODE12_1                     ((uint32_t)0x00020000) /* Bit 1 */

#define GPIO_CFGHR_MODE13                       ((uint32_t)0x00300000) /* MODE13[1:0] bits (Port x mode bits, pin 13) */
#define GPIO_CFGHR_MODE13_0                     ((uint32_t)0x00100000) /* Bit 0 */
#define GPIO_CFGHR_MODE13_1                     ((uint32_t)0x00200000) /* Bit 1 */

#define GPIO_CFGHR_MODE14                       ((uint32_t)0x03000000) /* MODE14[1:0] bits (Port x mode bits, pin 14) */
#define GPIO_CFGHR_MODE14_0                     ((uint32_t)0x01000000) /* Bit 0 */
#define GPIO_CFGHR_MODE14_1                     ((uint32_t)0x02000000) /* Bit 1 */

#define GPIO_CFGHR_MODE15                       ((uint32_t)0x30000000) /* MODE15[1:0] bits (Port x mode bits, pin 15) */
#define GPIO_CFGHR_MODE15_0                     ((uint32_t)0x10000000) /* Bit 0 */
#define GPIO_CFGHR_MODE15_1                     ((uint32_t)0x20000000) /* Bit 1 */

#define GPIO_CFGHR_CNF                          ((uint32_t)0xCCCCCCCC) /* Port x configuration bits */

#define GPIO_CFGHR_CNF8                         ((uint32_t)0x0000000C) /* CNF8[1:0] bits (Port x configuration bits, pin 8) */
#define GPIO_CFGHR_CNF8_0                       ((uint32_t)0x00000004) /* Bit 0 */
#define GPIO_CFGHR_CNF8_1                       ((uint32_t)0x00000008) /* Bit 1 */

#define GPIO_CFGHR_CNF9                         ((uint32_t)0x000000C0) /* CNF9[1:0] bits (Port x configuration bits, pin 9) */
#define GPIO_CFGHR_CNF9_0                       ((uint32_t)0x00000040) /* Bit 0 */
#define GPIO_CFGHR_CNF9_1                       ((uint32_t)0x00000080) /* Bit 1 */

#define GPIO_CFGHR_CNF10                        ((uint32_t)0x00000C00) /* CNF10[1:0] bits (Port x configuration bits, pin 10) */
#define GPIO_CFGHR_CNF10_0                      ((uint32_t)0x00000400) /* Bit 0 */
#define GPIO_CFGHR_CNF10_1                      ((uint32_t)0x00000800) /* Bit 1 */

#define GPIO_CFGHR_CNF11                        ((uint32_t)0x0000C000) /* CNF11[1:0] bits (Port x configuration bits, pin 11) */
#define GPIO_CFGHR_CNF11_0                      ((uint32_t)0x00004000) /* Bit 0 */
#define GPIO_CFGHR_CNF11_1                      ((uint32_t)0x00008000) /* Bit 1 */

#define GPIO_CFGHR_CNF12                        ((uint32_t)0x000C0000) /* CNF12[1:0] bits (Port x configuration bits, pin 12) */
#define GPIO_CFGHR_CNF12_0                      ((uint32_t)0x00040000) /* Bit 0 */
#define GPIO_CFGHR_CNF12_1                      ((uint32_t)0x00080000) /* Bit 1 */

#define GPIO_CFGHR_CNF13                        ((uint32_t)0x00C00000) /* CNF13[1:0] bits (Port x configuration bits, pin 13) */
#define GPIO_CFGHR_CNF13_0                      ((uint32_t)0x00400000) /* Bit 0 */
#define GPIO_CFGHR_CNF13_1                      ((uint32_t)0x00800000) /* Bit 1 */

#define GPIO_CFGHR_CNF14                        ((uint32_t)0x0C000000) /* CNF14[1:0] bits (Port x configuration bits, pin 14) */
#define GPIO_CFGHR_CNF14_0                      ((uint32_t)0x04000000) /* Bit 0 */
#define GPIO_CFGHR_CNF14_1                      ((uint32_t)0x08000000) /* Bit 1 */

#define GPIO_CFGHR_CNF15                        ((uint32_t)0xC0000000) /* CNF15[1:0] bits (Port x configuration bits, pin 15) */
#define GPIO_CFGHR_CNF15_0                      ((uint32_t)0x40000000) /* Bit 0 */
#define GPIO_CFGHR_CNF15_1                      ((uint32_t)0x80000000) /* Bit 1 */

/*******************  Bit definition for GPIO_INDR register  *******************/
#define GPIO_INDR_IDR0                          ((uint16_t)0x0001) /* Port input data, bit 0 */
#define GPIO_INDR_IDR1                          ((uint16_t)0x0002) /* Port input data, bit 1 */
#define GPIO_INDR_IDR2                          ((uint16_t)0x0004) /* Port input data, bit 2 */
#define GPIO_INDR_IDR3                          ((uint16_t)0x0008) /* Port input data, bit 3 */
#define GPIO_INDR_IDR4                          ((uint16_t)0x0010) /* Port input data, bit 4 */
#define GPIO_INDR_IDR5                          ((uint16_t)0x0020) /* Port input data, bit 5 */
#define GPIO_INDR_IDR6                          ((uint16_t)0x0040) /* Port input data, bit 6 */
#define GPIO_INDR_IDR7                          ((uint16_t)0x0080) /* Port input data, bit 7 */
#define GPIO_INDR_IDR8                          ((uint16_t)0x0100) /* Port input data, bit 8 */
#define GPIO_INDR_IDR9                          ((uint16_t)0x0200) /* Port input data, bit 9 */
#define GPIO_INDR_IDR10                         ((uint16_t)0x0400) /* Port input data, bit 10 */
#define GPIO_INDR_IDR11                         ((uint16_t)0x0800) /* Port input data, bit 11 */
#define GPIO_INDR_IDR12                         ((uint16_t)0x1000) /* Port input data, bit 12 */
#define GPIO_INDR_IDR13                         ((uint16_t)0x2000) /* Port input data, bit 13 */
#define GPIO_INDR_IDR14                         ((uint16_t)0x4000) /* Port input data, bit 14 */
#define GPIO_INDR_IDR15                         ((uint16_t)0x8000) /* Port input data, bit 15 */

/*******************  Bit definition for GPIO_OUTDR register  *******************/
#define GPIO_OUTDR_ODR0                         ((uint16_t)0x0001) /* Port output data, bit 0 */
#define GPIO_OUTDR_ODR1                         ((uint16_t)0x0002) /* Port output data, bit 1 */
#define GPIO_OUTDR_ODR2                         ((uint16_t)0x0004) /* Port output data, bit 2 */
#define GPIO_OUTDR_ODR3                         ((uint16_t)0x0008) /* Port output data, bit 3 */
#define GPIO_OUTDR_ODR4                         ((uint16_t)0x0010) /* Port output data, bit 4 */
#define GPIO_OUTDR_ODR5                         ((uint16_t)0x0020) /* Port output data, bit 5 */
#define GPIO_OUTDR_ODR6                         ((uint16_t)0x0040) /* Port output data, bit 6 */
#define GPIO_OUTDR_ODR7                         ((uint16_t)0x0080) /* Port output data, bit 7 */
#define GPIO_OUTDR_ODR8                         ((uint16_t)0x0100) /* Port output data, bit 8 */
#define GPIO_OUTDR_ODR9                         ((uint16_t)0x0200) /* Port output data, bit 9 */
#define GPIO_OUTDR_ODR10                        ((uint16_t)0x0400) /* Port output data, bit 10 */
#define GPIO_OUTDR_ODR11                        ((uint16_t)0x0800) /* Port output data, bit 11 */
#define GPIO_OUTDR_ODR12                        ((uint16_t)0x1000) /* Port output data, bit 12 */
#define GPIO_OUTDR_ODR13                        ((uint16_t)0x2000) /* Port output data, bit 13 */
#define GPIO_OUTDR_ODR14                        ((uint16_t)0x4000) /* Port output data, bit 14 */
#define GPIO_OUTDR_ODR15                        ((uint16_t)0x8000) /* Port output data, bit 15 */

/******************  Bit definition for GPIO_BSHR register  *******************/
#define GPIO_BSHR_BS0                           ((uint32_t)0x00000001) /* Port x Set bit 0 */
#define GPIO_BSHR_BS1                           ((uint32_t)0x00000002) /* Port x Set bit 1 */
#define GPIO_BSHR_BS2                           ((uint32_t)0x00000004) /* Port x Set bit 2 */
#define GPIO_BSHR_BS3                           ((uint32_t)0x00000008) /* Port x Set bit 3 */
#define GPIO_BSHR_BS4                           ((uint32_t)0x00000010) /* Port x Set bit 4 */
#define GPIO_BSHR_BS5                           ((uint32_t)0x00000020) /* Port x Set bit 5 */
#define GPIO_BSHR_BS6                           ((uint32_t)0x00000040) /* Port x Set bit 6 */
#define GPIO_BSHR_BS7                           ((uint32_t)0x00000080) /* Port x Set bit 7 */
#define GPIO_BSHR_BS8                           ((uint32_t)0x00000100) /* Port x Set bit 8 */
#define GPIO_BSHR_BS9                           ((uint32_t)0x00000200) /* Port x Set bit 9 */
#define GPIO_BSHR_BS10                          ((uint32_t)0x00000400) /* Port x Set bit 10 */
#define GPIO_BSHR_BS11                          ((uint32_t)0x00000800) /* Port x Set bit 11 */
#define GPIO_BSHR_BS12                          ((uint32_t)0x00001000) /* Port x Set bit 12 */
#define GPIO_BSHR_BS13                          ((uint32_t)0x00002000) /* Port x Set bit 13 */
#define GPIO_BSHR_BS14                          ((uint32_t)0x00004000) /* Port x Set bit 14 */
#define GPIO_BSHR_BS15                          ((uint32_t)0x00008000) /* Port x Set bit 15 */

#define GPIO_BSHR_BR0                           ((uint32_t)0x00010000) /* Port x Reset bit 0 */
#define GPIO_BSHR_BR1                           ((uint32_t)0x00020000) /* Port x Reset bit 1 */
#define GPIO_BSHR_BR2                           ((uint32_t)0x00040000) /* Port x Reset bit 2 */
#define GPIO_BSHR_BR3                           ((uint32_t)0x00080000) /* Port x Reset bit 3 */
#define GPIO_BSHR_BR4                           ((uint32_t)0x00100000) /* Port x Reset bit 4 */
#define GPIO_BSHR_BR5                           ((uint32_t)0x00200000) /* Port x Reset bit 5 */
#define GPIO_BSHR_BR6                           ((uint32_t)0x00400000) /* Port x Reset bit 6 */
#define GPIO_BSHR_BR7                           ((uint32_t)0x00800000) /* Port x Reset bit 7 */
#define GPIO_BSHR_BR8                           ((uint32_t)0x01000000) /* Port x Reset bit 8 */
#define GPIO_BSHR_BR9                           ((uint32_t)0x02000000) /* Port x Reset bit 9 */
#define GPIO_BSHR_BR10                          ((uint32_t)0x04000000) /* Port x Reset bit 10 */
#define GPIO_BSHR_BR11                          ((uint32_t)0x08000000) /* Port x Reset bit 11 */
#define GPIO_BSHR_BR12                          ((uint32_t)0x10000000) /* Port x Reset bit 12 */
#define GPIO_BSHR_BR13                          ((uint32_t)0x20000000) /* Port x Reset bit 13 */
#define GPIO_BSHR_BR14                          ((uint32_t)0x40000000) /* Port x Reset bit 14 */
#define GPIO_BSHR_BR15                          ((uint32_t)0x80000000) /* Port x Reset bit 15 */

/*******************  Bit definition for GPIO_BCR register  *******************/
#define GPIO_BCR_BR0                            ((uint16_t)0x0001) /* Port x Reset bit 0 */
#define GPIO_BCR_BR1                            ((uint16_t)0x0002) /* Port x Reset bit 1 */
#define GPIO_BCR_BR2                            ((uint16_t)0x0004) /* Port x Reset bit 2 */
#define GPIO_BCR_BR3                            ((uint16_t)0x0008) /* Port x Reset bit 3 */
#define GPIO_BCR_BR4                            ((uint16_t)0x0010) /* Port x Reset bit 4 */
#define GPIO_BCR_BR5                            ((uint16_t)0x0020) /* Port x Reset bit 5 */
#define GPIO_BCR_BR6                            ((uint16_t)0x0040) /* Port x Reset bit 6 */
#define GPIO_BCR_BR7                            ((uint16_t)0x0080) /* Port x Reset bit 7 */
#define GPIO_BCR_BR8                            ((uint16_t)0x0100) /* Port x Reset bit 8 */
#define GPIO_BCR_BR9                            ((uint16_t)0x0200) /* Port x Reset bit 9 */
#define GPIO_BCR_BR10                           ((uint16_t)0x0400) /* Port x Reset bit 10 */
#define GPIO_BCR_BR11                           ((uint16_t)0x0800) /* Port x Reset bit 11 */
#define GPIO_BCR_BR12                           ((uint16_t)0x1000) /* Port x Reset bit 12 */
#define GPIO_BCR_BR13                           ((uint16_t)0x2000) /* Port x Reset bit 13 */
#define GPIO_BCR_BR14                           ((uint16_t)0x4000) /* Port x Reset bit 14 */
#define GPIO_BCR_BR15                           ((uint16_t)0x8000) /* Port x Reset bit 15 */

/******************  Bit definition for GPIO_LCKR register  *******************/
#define GPIO_LCK0                               ((uint32_t)0x00000001) /* Port x Lock bit 0 */
#define GPIO_LCK1                               ((uint32_t)0x00000002) /* Port x Lock bit 1 */
#define GPIO_LCK2                               ((uint32_t)0x00000004) /* Port x Lock bit 2 */
#define GPIO_LCK3                               ((uint32_t)0x00000008) /* Port x Lock bit 3 */
#define GPIO_LCK4                               ((uint32_t)0x00000010) /* Port x Lock bit 4 */
#define GPIO_LCK5                               ((uint32_t)0x00000020) /* Port x Lock bit 5 */
#define GPIO_LCK6                               ((uint32_t)0x00000040) /* Port x Lock bit 6 */
#define GPIO_LCK7                               ((uint32_t)0x00000080) /* Port x Lock bit 7 */
#define GPIO_LCK8                               ((uint32_t)0x00000100) /* Port x Lock bit 8 */
#define GPIO_LCK9                               ((uint32_t)0x00000200) /* Port x Lock bit 9 */
#define GPIO_LCK10                              ((uint32_t)0x00000400) /* Port x Lock bit 10 */
#define GPIO_LCK11                              ((uint32_t)0x00000800) /* Port x Lock bit 11 */
#define GPIO_LCK12                              ((uint32_t)0x00001000) /* Port x Lock bit 12 */
#define GPIO_LCK13                              ((uint32_t)0x00002000) /* Port x Lock bit 13 */
#define GPIO_LCK14                              ((uint32_t)0x00004000) /* Port x Lock bit 14 */
#define GPIO_LCK15                              ((uint32_t)0x00008000) /* Port x Lock bit 15 */
#define GPIO_LCKK                               ((uint32_t)0x00010000) /* Lock key */

/******************  Bit definition for AFIO_PCFR1 register  *******************/
#define AFIO_PCFR1_SPI1_REMAP                   ((uint32_t)0x00000001) /* SPI1 remapping */

#define AFIO_PCFR1_I2C1_REMAP                   ((uint32_t)0x00400002) /* I2C1 remapping */
#define AFIO_PCFR1_I2C1_REMAP_0                 ((uint32_t)0x00000002) /* bit 0 */
#define AFIO_PCFR1_I2C1_REMAP_1                 ((uint32_t)0x00400000) /* bit 1 */

#define AFIO_PCFR1_I2C1_REMAP_NOREMAP         ((uint32_t)0x00000000) /* No remap (SCL/PC2, SDA/PC1) */
#define AFIO_PCFR1_I2C1_REMAP_REMAP1          ((uint32_t)0x00000002) /* remap 1 (SCL/PD1, SDA/PD0) */
#define AFIO_PCFR1_I2C1_REMAP_REMAP2          ((uint32_t)0x00400000) /* remap 2 (SCL/PC5, SDA/PC6) */

#define AFIO_PCFR1_USART1_REMAP                 ((uint32_t)0x00200004) /* USART1 remapping */
#define AFIO_PCFR1_USART1_REMAP_0               ((uint32_t)0x00000004) /* USART1 remapping low bit */
#define AFIO_PCFR1_USART1_REMAP_1               ((uint32_t)0x00200000) /* USART1 remapping high bit */

#define AFIO_PCFR1_USART1_REMAP_NOREMAP         ((uint32_t)0x00000000) /* No remap (CK/PD4, TX/PD5, RX/PD6, CTS/PD3, RTS/PC2) */
#define AFIO_PCFR1_USART1_REMAP_REMAP1          ((uint32_t)0x00000004) /* remap 1 (CK/PD7, TX/PD0, RX/PD1, CTS/PC3, RTS/PC2, SW_RX/PD0) */
#define AFIO_PCFR1_USART1_REMAP_REMAP2          ((uint32_t)0x00200000) /* remap 2 (CK/PD7, TX/PD6, RX/PD5, CTS/PC6, RTS/PC7, SW_RX/PD6) */
#define AFIO_PCFR1_USART1_REMAP_REMAP3          ((uint32_t)0x00200004) /* remap 3 (CK/PC5, TX/PC0, RX/PC1, CTS/PC6, RTS/PC7, SW_RX/PC0)) */

#define AFIO_PCFR1_TIM1_REMAP                   ((uint32_t)0x000000C0) /* TIM1_REMAP[1:0] bits (TIM1 remapping) */
#define AFIO_PCFR1_TIM1_REMAP_0                 ((uint32_t)0x00000040) /* Bit 0 */
#define AFIO_PCFR1_TIM1_REMAP_1                 ((uint32_t)0x00000080) /* Bit 1 */

#define AFIO_PCFR1_TIM1_IREMAP                  ((uint32_t)0x00800000) /* TIM1 channel 1 selection: 1 - LSI clock; 0 - external pins. */

#define AFIO_PCFR1_TIM1_REMAP_NOREMAP           ((uint32_t)0x00000000) /* No remap (ETR/PA12, CH1/PA8, CH2/PA9, CH3/PA10, CH4/PA11, BKIN/PB12, CH1N/PB13, CH2N/PB14, CH3N/PB15) */
#define AFIO_PCFR1_TIM1_REMAP_PARTIALREMAP      ((uint32_t)0x00000040) /* Partial remap (ETR/PA12, CH1/PA8, CH2/PA9, CH3/PA10, CH4/PA11, BKIN/PA6, CH1N/PA7, CH2N/PB0, CH3N/PB1) */
#define AFIO_PCFR1_TIM1_REMAP_FULLREMAP         ((uint32_t)0x000000C0) /* Full remap (ETR/PE7, CH1/PE9, CH2/PE11, CH3/PE13, CH4/PE14, BKIN/PE15, CH1N/PE8, CH2N/PE10, CH3N/PE12) */

#define AFIO_PCFR1_TIM2_REMAP                   ((uint32_t)0x00000300) /* TIM2_REMAP[1:0] bits (TIM2 remapping) */
#define AFIO_PCFR1_TIM2_REMAP_0                 ((uint32_t)0x00000100) /* Bit 0 */
#define AFIO_PCFR1_TIM2_REMAP_1                 ((uint32_t)0x00000200) /* Bit 1 */

#define AFIO_PCFR1_TIM2_REMAP_NOREMAP           ((uint32_t)0x00000000) /* No remap (CH1/ETR/PA0, CH2/PA1, CH3/PA2, CH4/PA3) */
#define AFIO_PCFR1_TIM2_REMAP_PARTIALREMAP1     ((uint32_t)0x00000100) /* Partial remap (CH1/ETR/PA15, CH2/PB3, CH3/PA2, CH4/PA3) */
#define AFIO_PCFR1_TIM2_REMAP_PARTIALREMAP2     ((uint32_t)0x00000200) /* Partial remap (CH1/ETR/PA0, CH2/PA1, CH3/PB10, CH4/PB11) */
#define AFIO_PCFR1_TIM2_REMAP_FULLREMAP         ((uint32_t)0x00000300) /* Full remap (CH1/ETR/PA15, CH2/PB3, CH3/PB10, CH4/PB11) */

#define AFIO_PCFR1_PA12_REMAP                   ((uint32_t)0x00008000) /* Port D0/Port D1 mapping on OSC_IN/OSC_OUT */
#define AFIO_PCFR1_ADC1_ETRGINJ_REMAP           ((uint32_t)0x00020000) /* ADC 1 External Trigger Injected Conversion remapping */
#define AFIO_PCFR1_ADC1_ETRGREG_REMAP           ((uint32_t)0x00040000) /* ADC 1 External Trigger Regular Conversion remapping */

#define AFIO_PCFR1_SWJ_CFG                      ((uint32_t)0x07000000) /* SWJ_CFG[2:0] bits (Serial Wire JTAG configuration) */
#define AFIO_PCFR1_SWJ_CFG_0                    ((uint32_t)0x01000000) /* Bit 0 */
#define AFIO_PCFR1_SWJ_CFG_1                    ((uint32_t)0x02000000) /* Bit 1 */
#define AFIO_PCFR1_SWJ_CFG_2                    ((uint32_t)0x04000000) /* Bit 2 */

#define AFIO_PCFR1_SWJ_CFG_RESET                ((uint32_t)0x00000000) /* Full SWJ (JTAG-DP + SW-DP) : Reset State */
#define AFIO_PCFR1_SWJ_CFG_NOJNTRST             ((uint32_t)0x01000000) /* Full SWJ (JTAG-DP + SW-DP) but without JNTRST */
#define AFIO_PCFR1_SWJ_CFG_JTAGDISABLE          ((uint32_t)0x02000000) /* JTAG-DP Disabled and SW-DP Enabled */
#define AFIO_PCFR1_SWJ_CFG_DISABLE              ((uint32_t)0x04000000) /* JTAG-DP Disabled and SW-DP Disabled */

/*****************  Bit definition for AFIO_EXTICR1 register  *****************/
#define AFIO_EXTICR_EXTI0                      ((uint16_t)0x0003) /* EXTI 0 configuration */
#define AFIO_EXTICR_EXTI1                      ((uint16_t)0x000C) /* EXTI 1 configuration */
#define AFIO_EXTICR_EXTI2                      ((uint16_t)0x0030) /* EXTI 2 configuration */
#define AFIO_EXTICR_EXTI3                      ((uint16_t)0x00C0) /* EXTI 3 configuration */
#define AFIO_EXTICR_EXTI4                      ((uint16_t)0x0300) /* EXTI 3 configuration */
#define AFIO_EXTICR_EXTI5                      ((uint16_t)0x0C00) /* EXTI 3 configuration */
#define AFIO_EXTICR_EXTI6                      ((uint16_t)0x3000) /* EXTI 3 configuration */
#define AFIO_EXTICR_EXTI7                      ((uint16_t)0xC000) /* EXTI 3 configuration */

#define AFIO_EXTICR_EXTI0_PA                   ((uint16_t)0x0000) /* PA[0] pin */
// #define AFIO_EXTICR_EXTI0_PB                   ((uint16_t)0x0001) /* PB[0] pin */
#define AFIO_EXTICR_EXTI0_PC                   ((uint16_t)0x0002) /* PC[0] pin */
#define AFIO_EXTICR_EXTI0_PD                   ((uint16_t)0x0003) /* PD[0] pin */

#define AFIO_EXTICR_EXTI1_PA                   ((uint16_t)0x0000) /* PA[1] pin */
// #define AFIO_EXTICR_EXTI1_PB                   ((uint16_t)0x0004) /* PB[1] pin */
#define AFIO_EXTICR_EXTI1_PC                   ((uint16_t)0x0008) /* PC[1] pin */
#define AFIO_EXTICR_EXTI1_PD                   ((uint16_t)0x000C) /* PD[1] pin */

#define AFIO_EXTICR_EXTI2_PA                   ((uint16_t)0x0000) /* PA[2] pin */
// #define AFIO_EXTICR_EXTI2_PB                   ((uint16_t)0x0010) /* PB[2] pin */
#define AFIO_EXTICR_EXTI2_PC                   ((uint16_t)0x0020) /* PC[2] pin */
#define AFIO_EXTICR_EXTI2_PD                   ((uint16_t)0x0030) /* PD[2] pin */

#define AFIO_EXTICR_EXTI3_PA                   ((uint16_t)0x0000) /* PA[3] pin */
// #define AFIO_EXTICR_EXTI3_PB                   ((uint16_t)0x0040) /* PB[3] pin */
#define AFIO_EXTICR_EXTI3_PC                   ((uint16_t)0x0080) /* PC[3] pin */
#define AFIO_EXTICR_EXTI3_PD                   ((uint16_t)0x00C0) /* PD[3] pin */

#define AFIO_EXTICR_EXTI4_PA                   ((uint16_t)0x0000) /* PA[4] pin */
// #define AFIO_EXTICR_EXTI4_PB                   ((uint16_t)0x0100) /* PB[4] pin */
#define AFIO_EXTICR_EXTI4_PC                   ((uint16_t)0x0200) /* PC[4] pin */
#define AFIO_EXTICR_EXTI4_PD                   ((uint16_t)0x0300) /* PD[4] pin */

#define AFIO_EXTICR_EXTI5_PA                   ((uint16_t)0x0000) /* PA[5] pin */
// #define AFIO_EXTICR_EXTI5_PB                   ((uint16_t)0x0400) /* PB[5] pin */
#define AFIO_EXTICR_EXTI5_PC                   ((uint16_t)0x0800) /* PC[5] pin */
#define AFIO_EXTICR_EXTI5_PD                   ((uint16_t)0x0C00) /* PD[5] pin */

#define AFIO_EXTICR_EXTI6_PA                   ((uint16_t)0x0000) /* PA[6] pin */
// #define AFIO_EXTICR_EXTI6_PB                   ((uint16_t)0x1000) /* PB[6] pin */
#define AFIO_EXTICR_EXTI6_PC                   ((uint16_t)0x2000) /* PC[6] pin */
#define AFIO_EXTICR_EXTI6_PD                   ((uint16_t)0x3000) /* PD[6] pin */

#define AFIO_EXTICR_EXTI7_PA                   ((uint16_t)0x0000) /* PA[7] pin */
// #define AFIO_EXTICR_EXTI7_PB                   ((uint16_t)0x4000) /* PB[7] pin */
#define AFIO_EXTICR_EXTI7_PC                   ((uint16_t)0x8000) /* PC[7] pin */
#define AFIO_EXTICR_EXTI7_PD                   ((uint16_t)0xC000) /* PD[7] pin */

/******************************************************************************/
/*                           Independent WATCHDOG                             */
/******************************************************************************/

/*******************  Bit definition for IWDG_CTLR register  ********************/
#define IWDG_KEY                                ((uint16_t)0xFFFF) /* Key value (write only, read 0000h) */

/*******************  Bit definition for IWDG_PSCR register  ********************/
#define IWDG_PR                                 ((uint8_t)0x07) /* PR[2:0] (Prescaler divider) */
#define IWDG_PR_0                               ((uint8_t)0x01) /* Bit 0 */
#define IWDG_PR_1                               ((uint8_t)0x02) /* Bit 1 */
#define IWDG_PR_2                               ((uint8_t)0x04) /* Bit 2 */

/*******************  Bit definition for IWDG_RLDR register  *******************/
#define IWDG_RL                                 ((uint16_t)0x0FFF) /* Watchdog counter reload value */

/*******************  Bit definition for IWDG_STATR register  ********************/
#define IWDG_PVU                                ((uint8_t)0x01) /* Watchdog prescaler value update */
#define IWDG_RVU                                ((uint8_t)0x02) /* Watchdog counter reload value update */

/******************************************************************************/
/*                      Inter-integrated Circuit Interface                    */
/******************************************************************************/

/*******************  Bit definition for I2C_CTLR1 register  ********************/
#define I2C_CTLR1_PE                            ((uint16_t)0x0001) /* Peripheral Enable */
#define I2C_CTLR1_SMBUS                         ((uint16_t)0x0002) /* SMBus Mode */
#define I2C_CTLR1_SMBTYPE                       ((uint16_t)0x0008) /* SMBus Type */
#define I2C_CTLR1_ENARP                         ((uint16_t)0x0010) /* ARP Enable */
#define I2C_CTLR1_ENPEC                         ((uint16_t)0x0020) /* PEC Enable */
#define I2C_CTLR1_ENGC                          ((uint16_t)0x0040) /* General Call Enable */
#define I2C_CTLR1_NOSTRETCH                     ((uint16_t)0x0080) /* Clock Stretching Disable (Slave mode) */
#define I2C_CTLR1_START                         ((uint16_t)0x0100) /* Start Generation */
#define I2C_CTLR1_STOP                          ((uint16_t)0x0200) /* Stop Generation */
#define I2C_CTLR1_ACK                           ((uint16_t)0x0400) /* Acknowledge Enable */
#define I2C_CTLR1_POS                           ((uint16_t)0x0800) /* Acknowledge/PEC Position (for data reception) */
#define I2C_CTLR1_PEC                           ((uint16_t)0x1000) /* Packet Error Checking */
#define I2C_CTLR1_ALERT                         ((uint16_t)0x2000) /* SMBus Alert */
#define I2C_CTLR1_SWRST                         ((uint16_t)0x8000) /* Software Reset */

/*******************  Bit definition for I2C_CTLR2 register  ********************/
#define I2C_CTLR2_FREQ                          ((uint16_t)0x003F) /* FREQ[5:0] bits (Peripheral Clock Frequency) */
#define I2C_CTLR2_FREQ_0                        ((uint16_t)0x0001) /* Bit 0 */
#define I2C_CTLR2_FREQ_1                        ((uint16_t)0x0002) /* Bit 1 */
#define I2C_CTLR2_FREQ_2                        ((uint16_t)0x0004) /* Bit 2 */
#define I2C_CTLR2_FREQ_3                        ((uint16_t)0x0008) /* Bit 3 */
#define I2C_CTLR2_FREQ_4                        ((uint16_t)0x0010) /* Bit 4 */
#define I2C_CTLR2_FREQ_5                        ((uint16_t)0x0020) /* Bit 5 */

#define I2C_CTLR2_ITERREN                       ((uint16_t)0x0100) /* Error Interrupt Enable */
#define I2C_CTLR2_ITEVTEN                       ((uint16_t)0x0200) /* Event Interrupt Enable */
#define I2C_CTLR2_ITBUFEN                       ((uint16_t)0x0400) /* Buffer Interrupt Enable */
#define I2C_CTLR2_DMAEN                         ((uint16_t)0x0800) /* DMA Requests Enable */
#define I2C_CTLR2_LAST                          ((uint16_t)0x1000) /* DMA Last Transfer */

/*******************  Bit definition for I2C_OADDR1 register  *******************/
#define I2C_OADDR1_ADD1_7                       ((uint16_t)0x00FE) /* Interface Address */
#define I2C_OADDR1_ADD8_9                       ((uint16_t)0x0300) /* Interface Address */

#define I2C_OADDR1_ADD0                         ((uint16_t)0x0001) /* Bit 0 */
#define I2C_OADDR1_ADD1                         ((uint16_t)0x0002) /* Bit 1 */
#define I2C_OADDR1_ADD2                         ((uint16_t)0x0004) /* Bit 2 */
#define I2C_OADDR1_ADD3                         ((uint16_t)0x0008) /* Bit 3 */
#define I2C_OADDR1_ADD4                         ((uint16_t)0x0010) /* Bit 4 */
#define I2C_OADDR1_ADD5                         ((uint16_t)0x0020) /* Bit 5 */
#define I2C_OADDR1_ADD6                         ((uint16_t)0x0040) /* Bit 6 */
#define I2C_OADDR1_ADD7                         ((uint16_t)0x0080) /* Bit 7 */
#define I2C_OADDR1_ADD8                         ((uint16_t)0x0100) /* Bit 8 */
#define I2C_OADDR1_ADD9                         ((uint16_t)0x0200) /* Bit 9 */

#define I2C_OADDR1_ADDMODE                      ((uint16_t)0x8000) /* Addressing Mode (Slave mode) */

/*******************  Bit definition for I2C_OADDR2 register  *******************/
#define I2C_OADDR2_ENDUAL                       ((uint8_t)0x01) /* Dual addressing mode enable */
#define I2C_OADDR2_ADD2                         ((uint8_t)0xFE) /* Interface address */

/********************  Bit definition for I2C_DATAR register  ********************/
#define I2C_DR_DATAR                            ((uint8_t)0xFF) /* 8-bit Data Register */

/*******************  Bit definition for I2C_STAR1 register  ********************/
#define I2C_STAR1_SB                            ((uint16_t)0x0001) /* Start Bit (Master mode) */
#define I2C_STAR1_ADDR                          ((uint16_t)0x0002) /* Address sent (master mode)/matched (slave mode) */
#define I2C_STAR1_BTF                           ((uint16_t)0x0004) /* Byte Transfer Finished */
#define I2C_STAR1_ADD10                         ((uint16_t)0x0008) /* 10-bit header sent (Master mode) */
#define I2C_STAR1_STOPF                         ((uint16_t)0x0010) /* Stop detection (Slave mode) */
#define I2C_STAR1_RXNE                          ((uint16_t)0x0040) /* Data Register not Empty (receivers) */
#define I2C_STAR1_TXE                           ((uint16_t)0x0080) /* Data Register Empty (transmitters) */
#define I2C_STAR1_BERR                          ((uint16_t)0x0100) /* Bus Error */
#define I2C_STAR1_ARLO                          ((uint16_t)0x0200) /* Arbitration Lost (master mode) */
#define I2C_STAR1_AF                            ((uint16_t)0x0400) /* Acknowledge Failure */
#define I2C_STAR1_OVR                           ((uint16_t)0x0800) /* Overrun/Underrun */
#define I2C_STAR1_PECERR                        ((uint16_t)0x1000) /* PEC Error in reception */
#define I2C_STAR1_TIMEOUT                       ((uint16_t)0x4000) /* Timeout or Tlow Error */
#define I2C_STAR1_SMBALERT                      ((uint16_t)0x8000) /* SMBus Alert */

/*******************  Bit definition for I2C_STAR2 register  ********************/
#define I2C_STAR2_MSL                           ((uint16_t)0x0001) /* Master/Slave */
#define I2C_STAR2_BUSY                          ((uint16_t)0x0002) /* Bus Busy */
#define I2C_STAR2_TRA                           ((uint16_t)0x0004) /* Transmitter/Receiver */
#define I2C_STAR2_GENCALL                       ((uint16_t)0x0010) /* General Call Address (Slave mode) */
#define I2C_STAR2_SMBDEFAULT                    ((uint16_t)0x0020) /* SMBus Device Default Address (Slave mode) */
#define I2C_STAR2_SMBHOST                       ((uint16_t)0x0040) /* SMBus Host Header (Slave mode) */
#define I2C_STAR2_DUALF                         ((uint16_t)0x0080) /* Dual Flag (Slave mode) */
#define I2C_STAR2_PEC                           ((uint16_t)0xFF00) /* Packet Error Checking Register */

/*******************  Bit definition for I2C_CKCFGR register  ********************/
#define I2C_CKCFGR_CCR                          ((uint16_t)0x0FFF) /* Clock Control Register in Fast/Standard mode (Master mode) */
#define I2C_CKCFGR_DUTY                         ((uint16_t)0x4000) /* Fast Mode Duty Cycle */
#define I2C_CKCFGR_FS                           ((uint16_t)0x8000) /* I2C Master Mode Selection */

/******************************************************************************/
/*                             Power Control                                  */
/******************************************************************************/

/********************  Bit definition for PWR_CTLR register  ********************/
#define PWR_CTLR_LPDS                           ((uint16_t)0x0001) /* Low-Power Deepsleep */
#define PWR_CTLR_PDDS                           ((uint16_t)0x0002) /* Power Down Deepsleep */
#define PWR_CTLR_CWUF                           ((uint16_t)0x0004) /* Clear Wakeup Flag */
#define PWR_CTLR_CSBF                           ((uint16_t)0x0008) /* Clear Standby Flag */
#define PWR_CTLR_PVDE                           ((uint16_t)0x0010) /* Power Voltage Detector Enable */

#define PWR_CTLR_PLS                            ((uint16_t)0x00E0) /* PLS[2:0] bits (PVD Level Selection) */
#define PWR_CTLR_PLS_0                          ((uint16_t)0x0020) /* Bit 0 */
#define PWR_CTLR_PLS_1                          ((uint16_t)0x0040) /* Bit 1 */
#define PWR_CTLR_PLS_2                          ((uint16_t)0x0080) /* Bit 2 */

#define PWR_CTLR_PLS_2V2                        ((uint16_t)0x0000) /* PVD level 2.2V */
#define PWR_CTLR_PLS_2V3                        ((uint16_t)0x0020) /* PVD level 2.3V */
#define PWR_CTLR_PLS_2V4                        ((uint16_t)0x0040) /* PVD level 2.4V */
#define PWR_CTLR_PLS_2V5                        ((uint16_t)0x0060) /* PVD level 2.5V */
#define PWR_CTLR_PLS_2V6                        ((uint16_t)0x0080) /* PVD level 2.6V */
#define PWR_CTLR_PLS_2V7                        ((uint16_t)0x00A0) /* PVD level 2.7V */
#define PWR_CTLR_PLS_2V8                        ((uint16_t)0x00C0) /* PVD level 2.8V */
#define PWR_CTLR_PLS_2V9                        ((uint16_t)0x00E0) /* PVD level 2.9V */

#define PWR_CTLR_DBP                            ((uint16_t)0x0100) /* Disable Backup Domain write protection */

/*******************  Bit definition for PWR_CSR register  ********************/
#define PWR_CSR_WUF                             ((uint16_t)0x0001) /* Wakeup Flag */
#define PWR_CSR_SBF                             ((uint16_t)0x0002) /* Standby Flag */
#define PWR_CSR_PVDO                            ((uint16_t)0x0004) /* PVD Output */
#define PWR_CSR_EWUP                            ((uint16_t)0x0100) /* Enable WKUP pin */

/******************************************************************************/
/*                         Reset and Clock Control                            */
/******************************************************************************/

/********************  Bit definition for RCC_CTLR register  ********************/
#define RCC_HSION                               ((uint32_t)0x00000001) /* Internal High Speed clock enable */
#define RCC_HSIRDY                              ((uint32_t)0x00000002) /* Internal High Speed clock ready flag */
#define RCC_HSITRIM                             ((uint32_t)0x000000F8) /* Internal High Speed clock trimming */
#define RCC_HSICAL                              ((uint32_t)0x0000FF00) /* Internal High Speed clock Calibration */
#define RCC_HSEON                               ((uint32_t)0x00010000) /* External High Speed clock enable */
#define RCC_HSERDY                              ((uint32_t)0x00020000) /* External High Speed clock ready flag */
#define RCC_HSEBYP                              ((uint32_t)0x00040000) /* External High Speed clock Bypass */
#define RCC_CSSON                               ((uint32_t)0x00080000) /* Clock Security System enable */
#define RCC_PLLON                               ((uint32_t)0x01000000) /* PLL enable */
#define RCC_PLLRDY                              ((uint32_t)0x02000000) /* PLL clock ready flag */

/*******************  Bit definition for RCC_CFGR0 register  *******************/
#define RCC_SW                                  ((uint32_t)0x00000003) /* SW[1:0] bits (System clock Switch) */
#define RCC_SW_0                                ((uint32_t)0x00000001) /* Bit 0 */
#define RCC_SW_1                                ((uint32_t)0x00000002) /* Bit 1 */

#define RCC_SW_HSI                              ((uint32_t)0x00000000) /* HSI selected as system clock */
#define RCC_SW_HSE                              ((uint32_t)0x00000001) /* HSE selected as system clock */
#define RCC_SW_PLL                              ((uint32_t)0x00000002) /* PLL selected as system clock */

#define RCC_SWS                                 ((uint32_t)0x0000000C) /* SWS[1:0] bits (System Clock Switch Status) */
#define RCC_SWS_0                               ((uint32_t)0x00000004) /* Bit 0 */
#define RCC_SWS_1                               ((uint32_t)0x00000008) /* Bit 1 */

#define RCC_SWS_HSI                             ((uint32_t)0x00000000) /* HSI oscillator used as system clock */
#define RCC_SWS_HSE                             ((uint32_t)0x00000004) /* HSE oscillator used as system clock */
#define RCC_SWS_PLL                             ((uint32_t)0x00000008) /* PLL used as system clock */

#define RCC_HPRE                                ((uint32_t)0x000000F0) /* HPRE[3:0] bits (AHB prescaler) */
#define RCC_HPRE_0                              ((uint32_t)0x00000010) /* Bit 0 */
#define RCC_HPRE_1                              ((uint32_t)0x00000020) /* Bit 1 */
#define RCC_HPRE_2                              ((uint32_t)0x00000040) /* Bit 2 */
#define RCC_HPRE_3                              ((uint32_t)0x00000080) /* Bit 3 */
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
